ninicksicard/FFF_Free_Food_forever/docs/progression medias/100x+ spirulina microscope(streight strain) (1).jpg

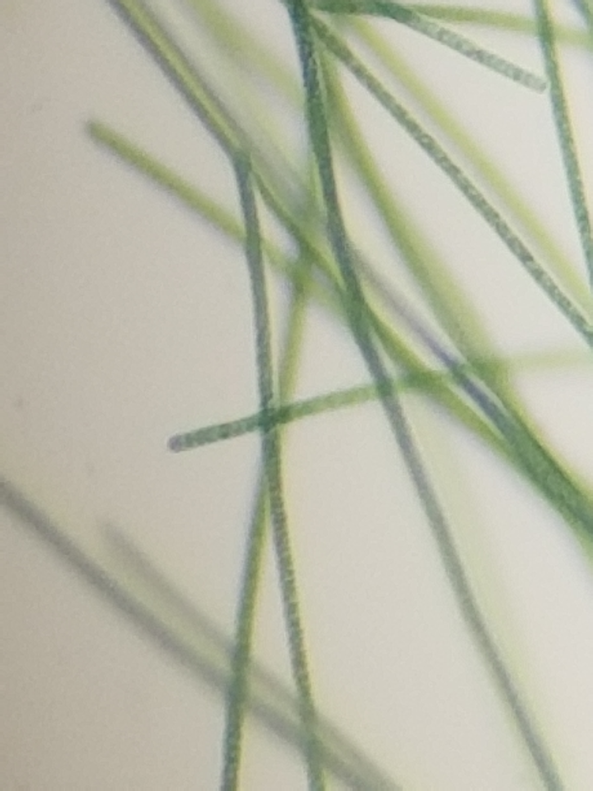
docs/progression medias/100x+ spirulina microscope(streight strain) (1).jpg
