ninicksicard/FFF_Free_Food_forever/docs/progression medias/100x+ spirulina microscope(streight strain) (2).jpg

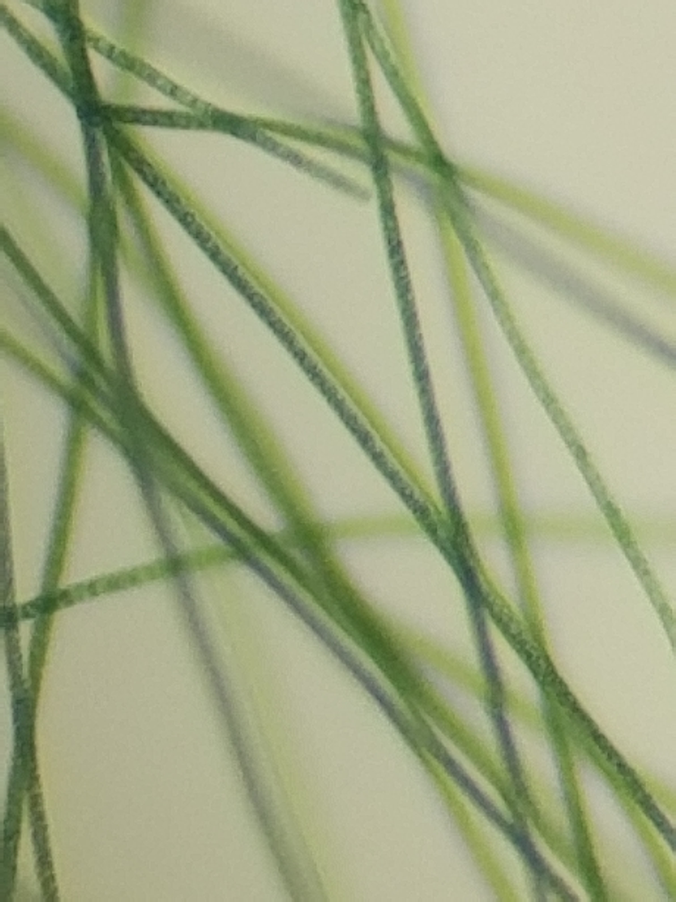
docs/progression medias/100x+ spirulina microscope(streight strain) (2).jpg
