ninicksicard/FFF_Free_Food_forever/docs/progression medias/20210616_152450.jpg

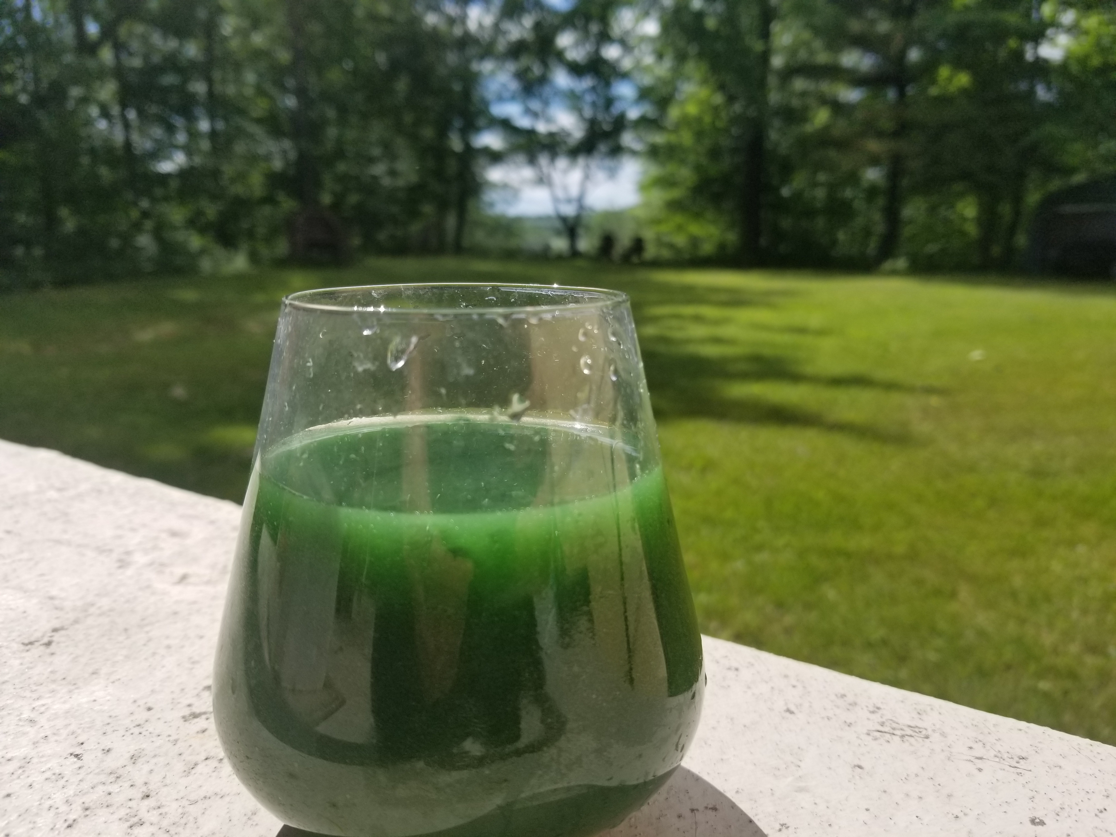
docs/progression medias/20210616_152450.jpg
