ninicksicard/FFF_Free_Food_forever/docs/progression medias/20210706_202033.jpg

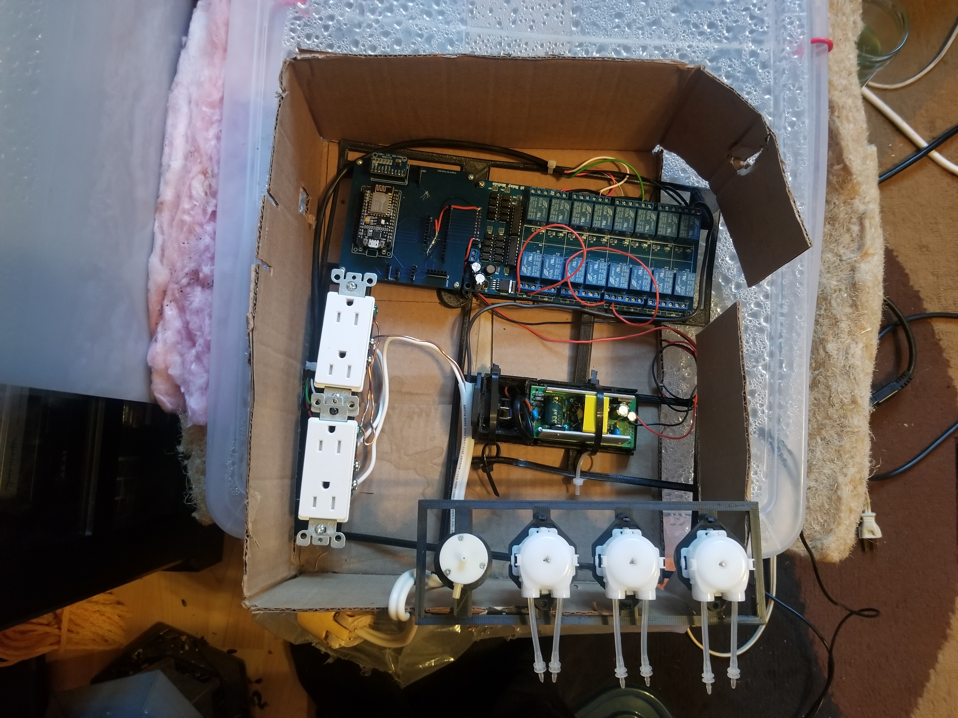
docs/progression medias/20210706_202033.jpg
