ninicksicard/FFF_Free_Food_forever/docs/progression medias/20210712_165235.jpg

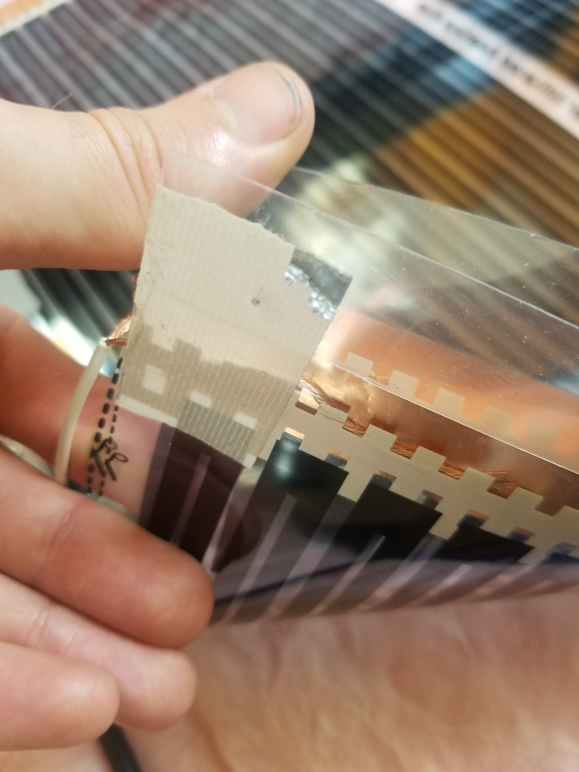
docs/progression medias/20210712_165235.jpg
