ninicksicard/FFF_Free_Food_forever/docs/progression medias/20210717_211324.jpg

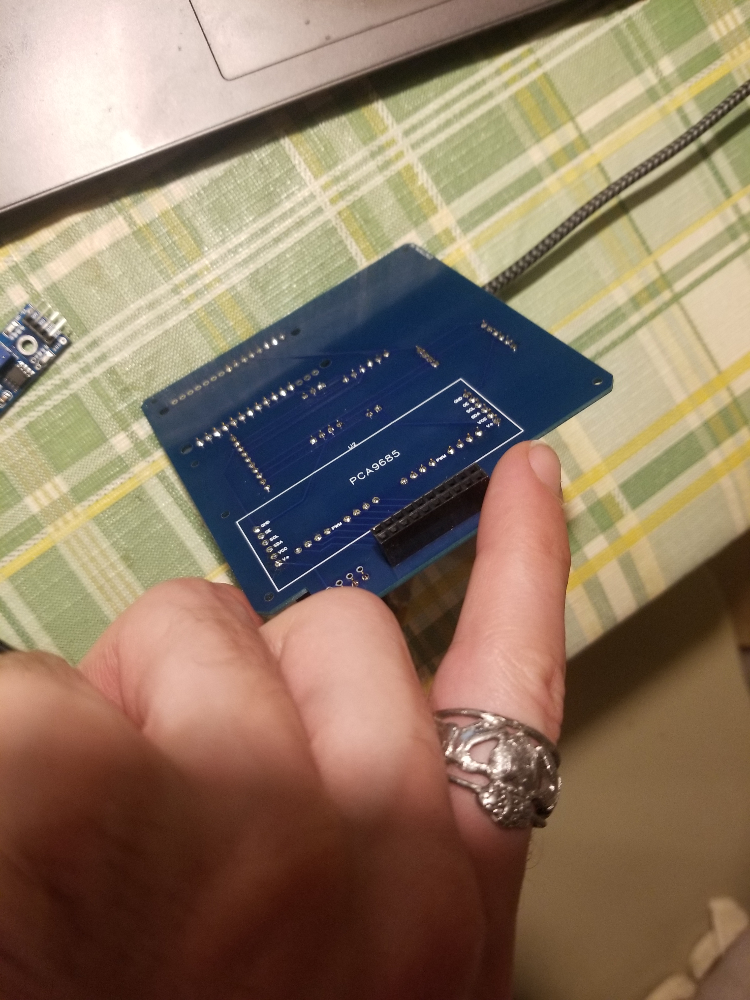
docs/progression medias/20210717_211324.jpg
