ninicksicard/FFF_Free_Food_forever/docs/progression medias/20210720_201423.jpg

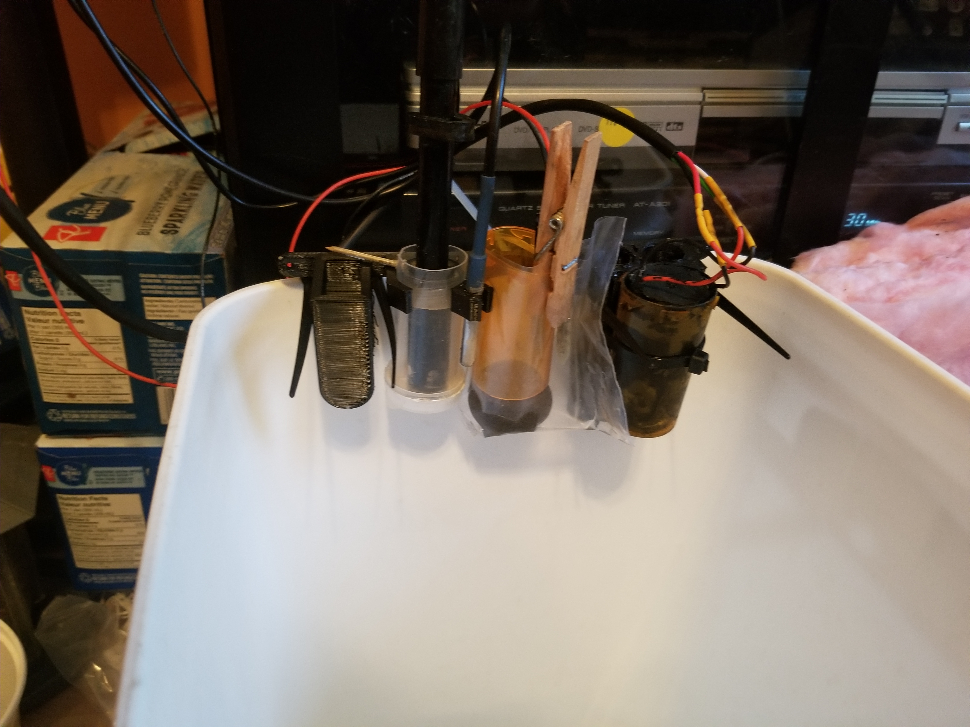
docs/progression medias/20210720_201423.jpg
