ninicksicard/FFF_Free_Food_forever/docs/progression medias/20210803_112624.jpg

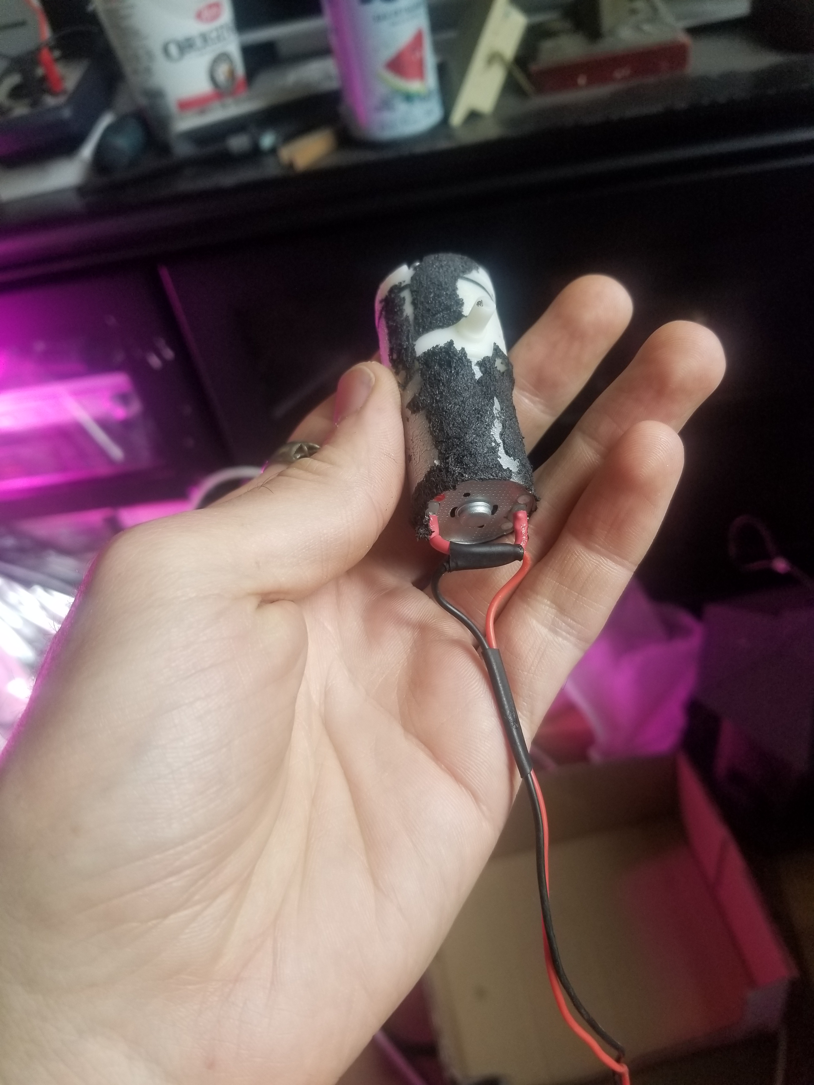
docs/progression medias/20210803_112624.jpg
