ninicksicard/FFF_Free_Food_forever/docs/progression medias/20220109_112840.jpg

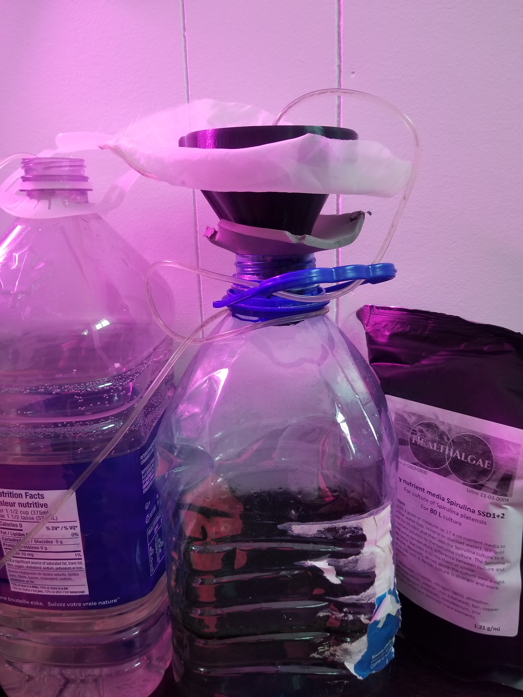
docs/progression medias/20220109_112840.jpg
