ninicksicard/FFF_Free_Food_forever/docs/progression medias/sample backup.jpg

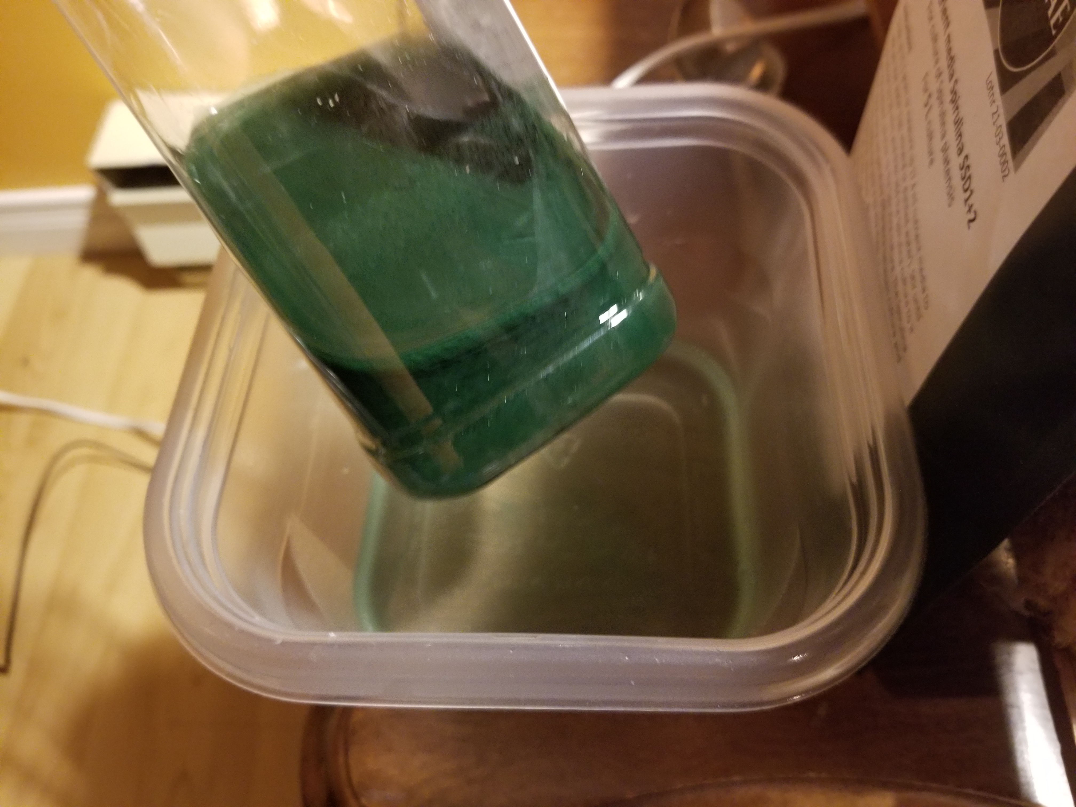
docs/progression medias/sample backup.jpg
