ninicksicard/FFF_Free_Food_forever/docs/progression medias/Screenshot_2.png

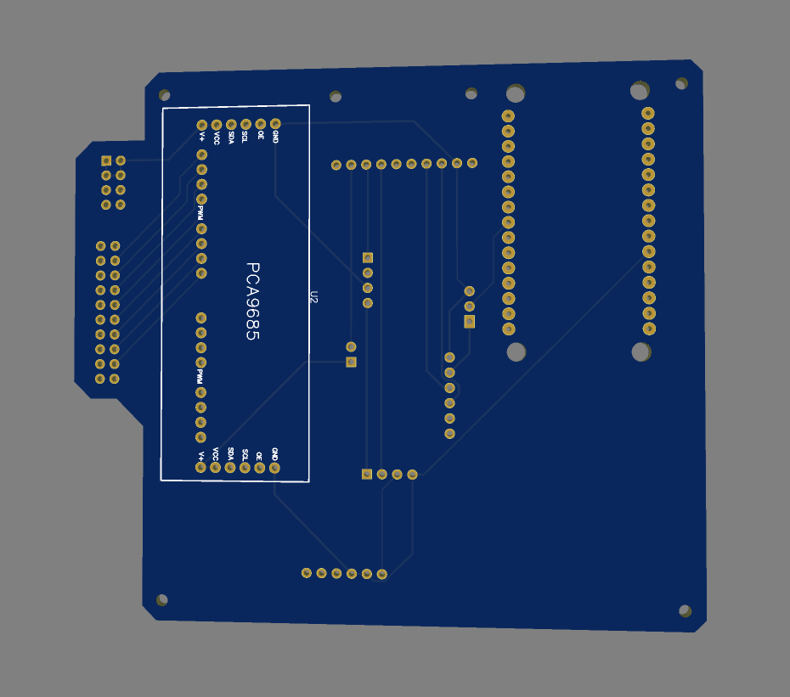
docs/progression medias/Screenshot_2.png
