ninicksicard/FFF_Free_Food_forever/docs/progression medias/Screenshot_4.png

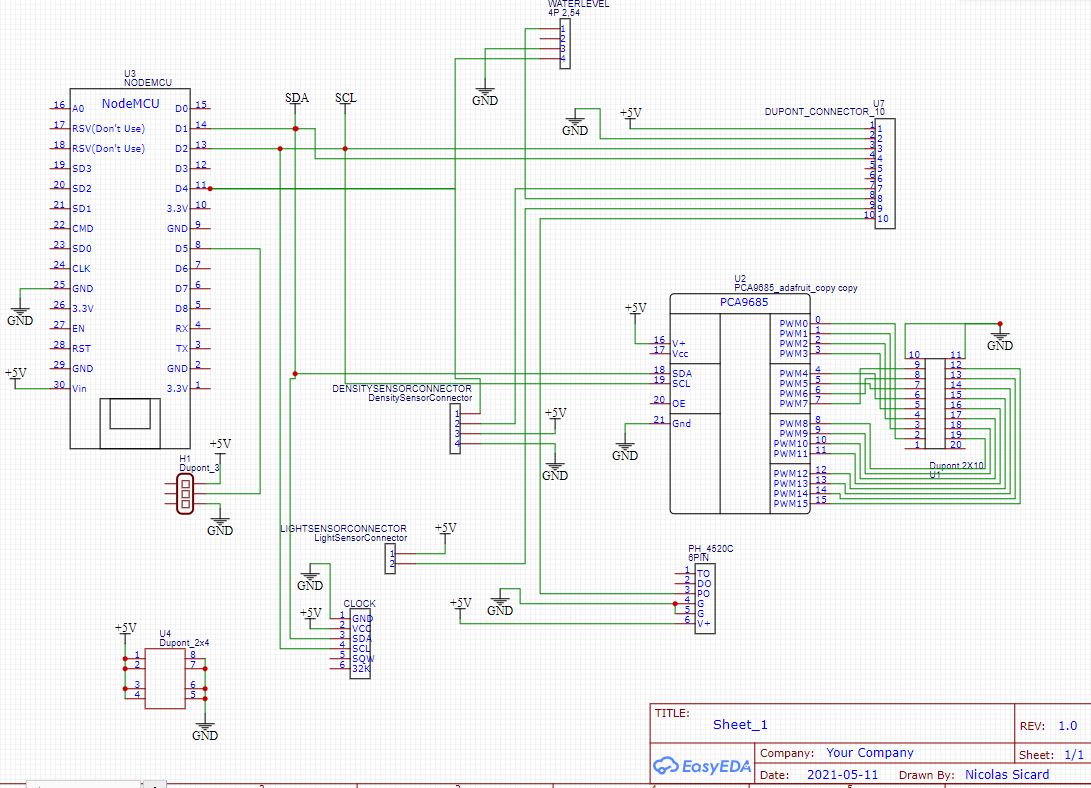
docs/progression medias/Screenshot_4.png
