ninicksicard/FFF_Free_Food_forever/Software/Screenshot_1.png

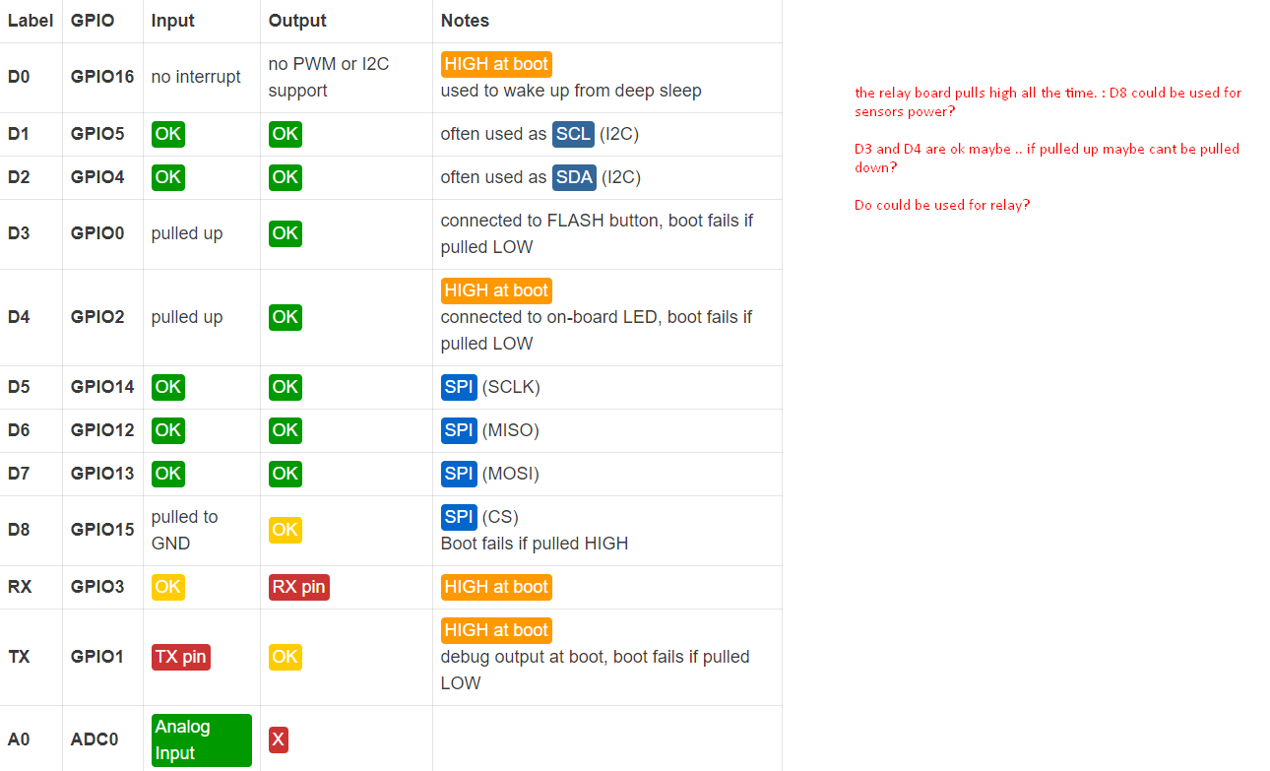
Software/Screenshot_1.png
