ninicksicard/FFF_Free_Food_forever/Hardware/STL/water_side - spacer_long-1.STL

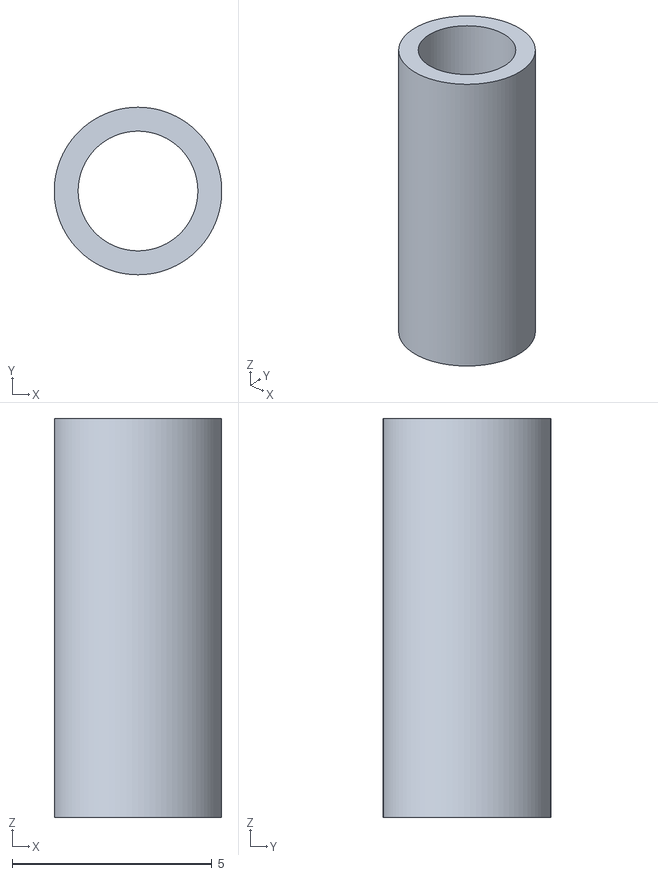
[picture p70: CAD file, 2022-02-06]
Hardware/STL/water_side - spacer_long-1.STL
4.20 x 4.20 x 10.0
