ninicksicard/FFF_Free_Food_forever/Hardware/STL/water_side - motor N20-2 spur gear_iso-4.STL

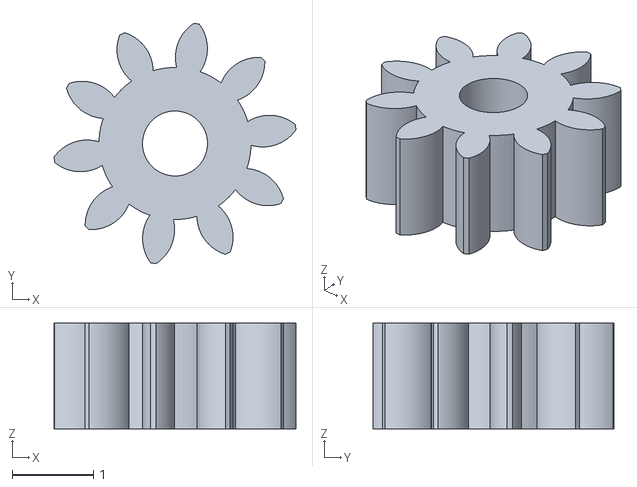
[picture p72: CAD file, 2022-02-06]
Hardware/STL/water_side - motor N20-2 spur gear_iso-4.STL
2.98 x 2.96 x 1.30
