ninicksicard/FFF_Free_Food_forever/Hardware/STL/water_side - spacer-1.STL

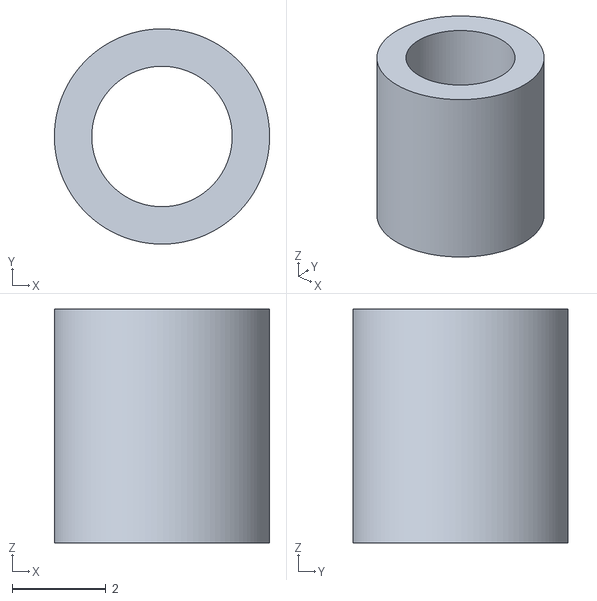
[picture p73: CAD file, 2022-02-06]
Hardware/STL/water_side - spacer-1.STL
4.60 x 4.60 x 5.00
