ninicksicard/FFF_Free_Food_forever/Hardware/STL/water_side - motor N20-2 втулка боковой шестерни-1.STL

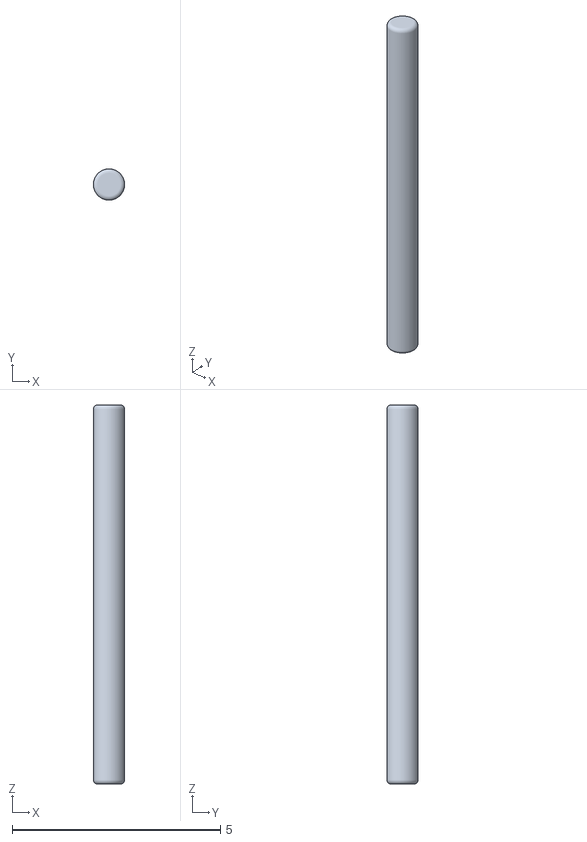
[picture p75: CAD file, 2022-02-06]
Hardware/STL/water_side - motor N20-2 втулка боковой шестерни-1.STL
0.75 x 0.75 x 9.10
