ninicksicard/FFF_Free_Food_forever/Hardware/STL/water_side - motor N20-2 spur gear_iso-9.STL

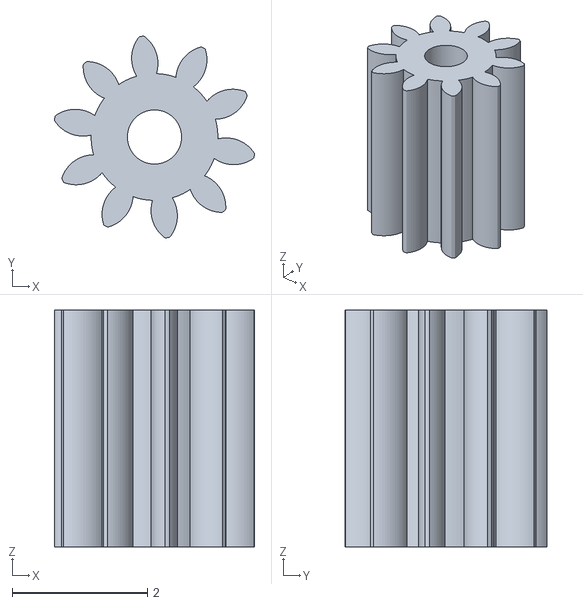
[picture p77: CAD file, 2022-02-06]
Hardware/STL/water_side - motor N20-2 spur gear_iso-9.STL
2.96 x 2.98 x 3.50
