ninicksicard/FFF_Free_Food_forever/Hardware/STL/water_side - motor N20-2 spur gear_iso-1.STL

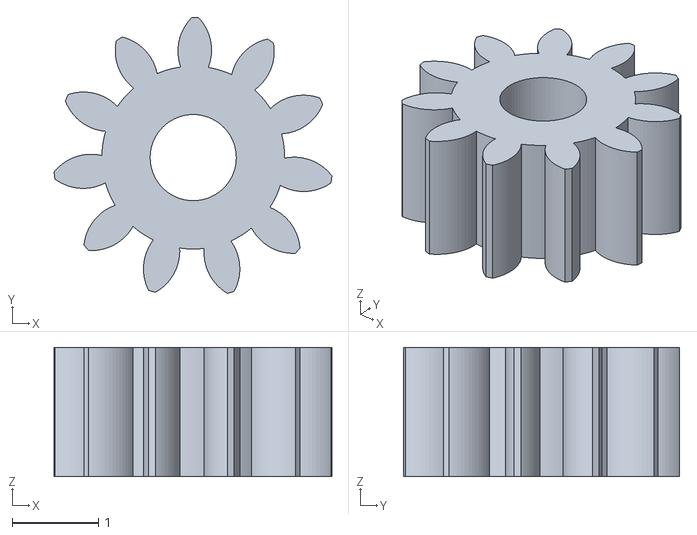
[picture p79: CAD file, 2022-02-06]
Hardware/STL/water_side - motor N20-2 spur gear_iso-1.STL
3.23 x 3.20 x 1.50
