ninicksicard/FFF_Free_Food_forever/Hardware/STL/water_side - motor N20-2 большая  фтулка-1.STL

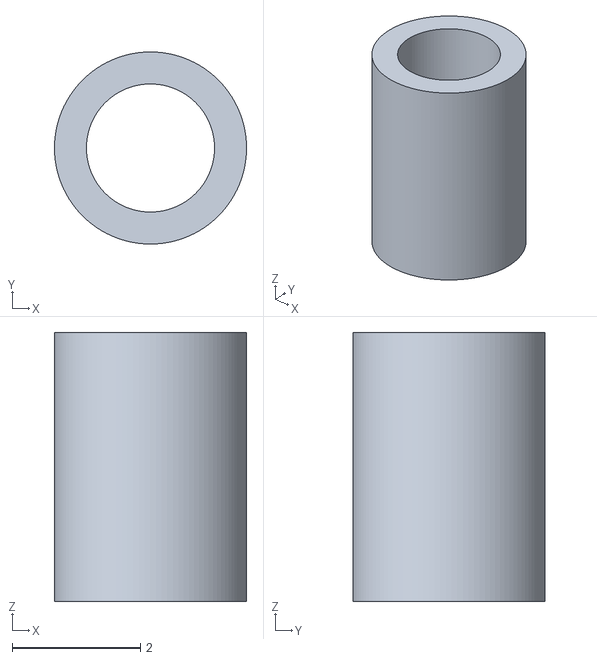
[picture p80: CAD file, 2022-02-06]
Hardware/STL/water_side - motor N20-2 большая фтулка-1.STL
3.00 x 3.00 x 4.20
