ninicksicard/FFF_Free_Food_forever/Hardware/STL/water_side - combinedmount-1.STL

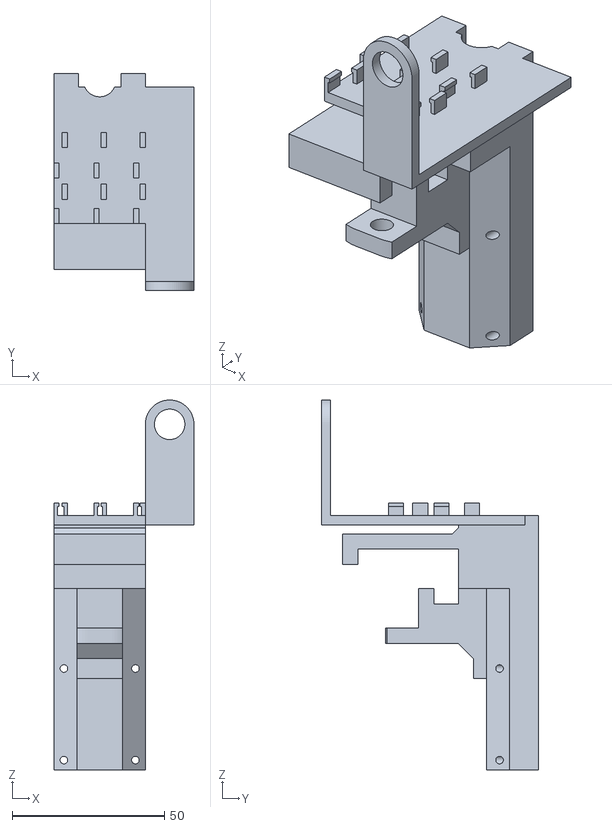
[picture p81: CAD file, 2022-02-06]
Hardware/STL/water_side - combinedmount-1.STL
46.0 x 71.4 x 121.6
