ninicksicard/FFF_Free_Food_forever/Hardware/STL/water_side - axel_connector-1.STL

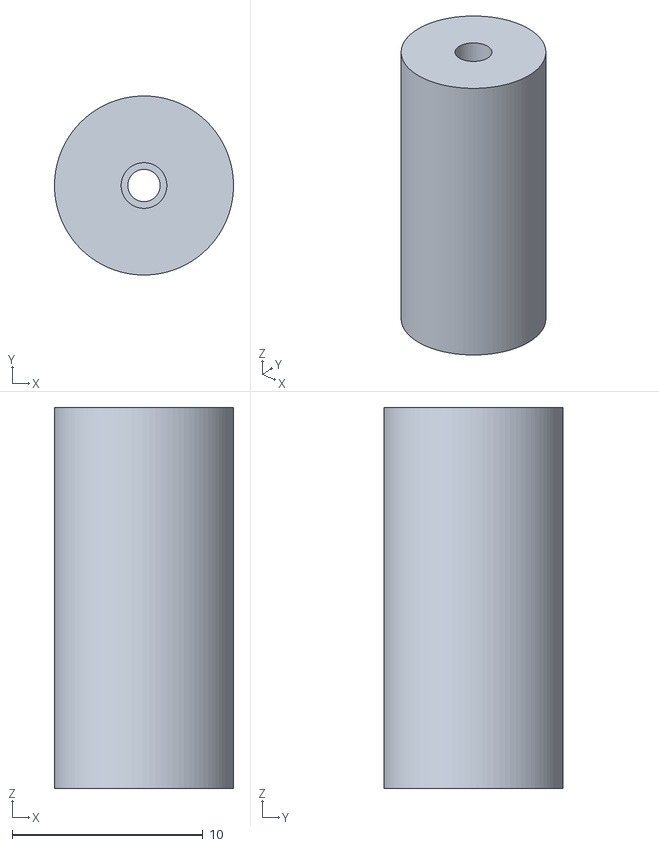
[picture p83: CAD file, 2022-02-06]
Hardware/STL/water_side - axel_connector-1.STL
9.40 x 9.40 x 20.0
