ninicksicard/FFF_Free_Food_forever/Hardware/STL/water_side - motor N20-2 верхняя пластина редуктора-1.STL

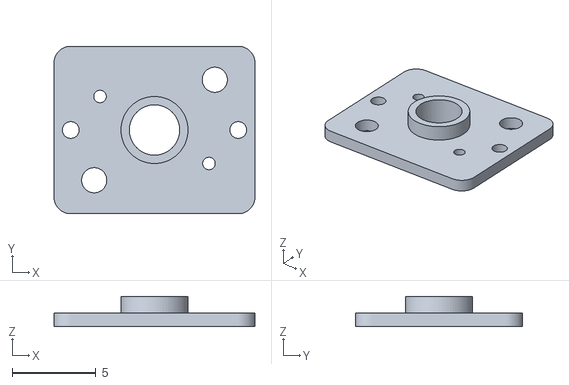
[picture p84: CAD file, 2022-02-06]
Hardware/STL/water_side - motor N20-2 верхняя пластина редуктора-1.STL
12.0 x 10.0 x 1.80
