ninicksicard/FFF_Free_Food_forever/Hardware/STL/water_side - Water_wheel_axel-1.STL

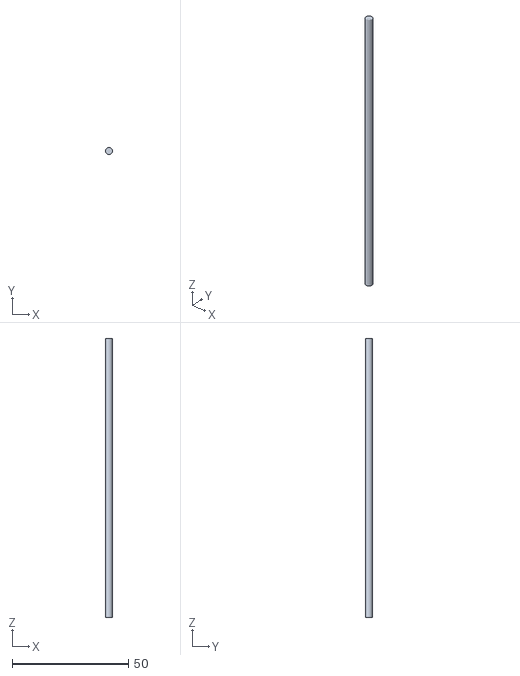
[picture p85: CAD file, 2022-02-06]
Hardware/STL/water_side - Water_wheel_axel-1.STL
3.00 x 3.00 x 120.0
