ninicksicard/FFF_Free_Food_forever/Hardware/STL/water_side - second_bearing_housing-1.STL

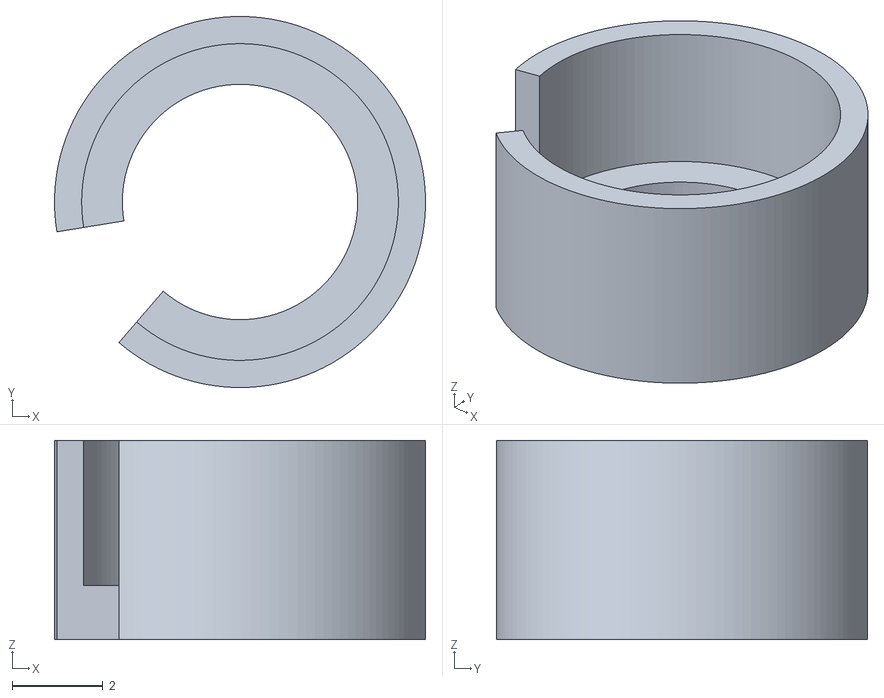
[picture p88: CAD file, 2022-02-06]
Hardware/STL/water_side - second_bearing_housing-1.STL
8.20 x 8.20 x 4.40
