ninicksicard/FFF_Free_Food_forever/Hardware/STL/water_side - motor N20-2 spur gear_iso-3.STL

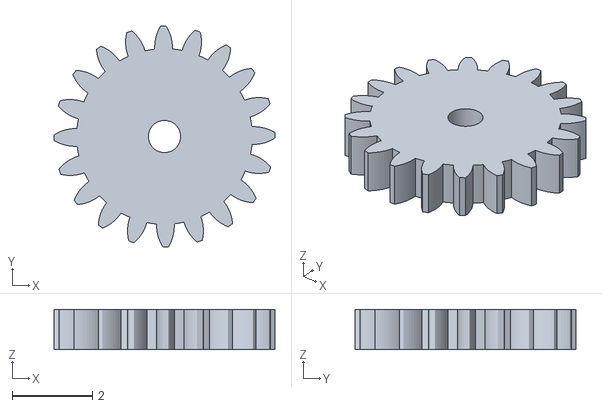
[picture p89: CAD file, 2022-02-06]
Hardware/STL/water_side - motor N20-2 spur gear_iso-3.STL
5.50 x 5.50 x 1.00
