ninicksicard/FFF_Free_Food_forever/Hardware/STL/water_side - bearing_mount-1.STL

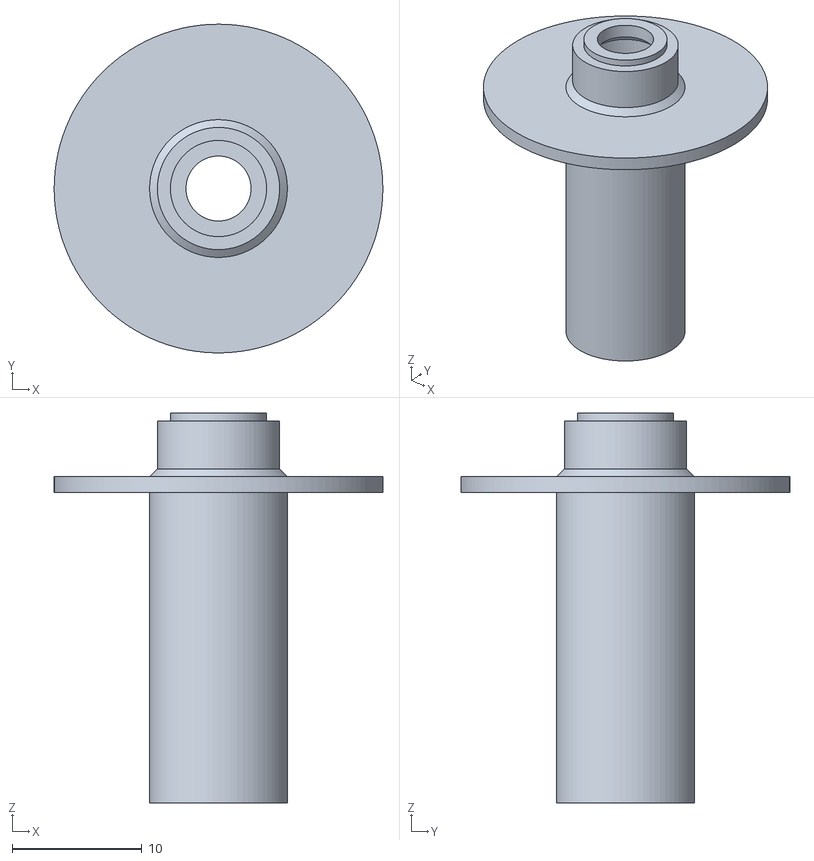
[picture p90: CAD file, 2022-02-06]
Hardware/STL/water_side - bearing_mount-1.STL
25.3 x 25.3 x 30.0
