ninicksicard/FFF_Free_Food_forever/Hardware/STL/System - highvoltage cable routing-1.STL

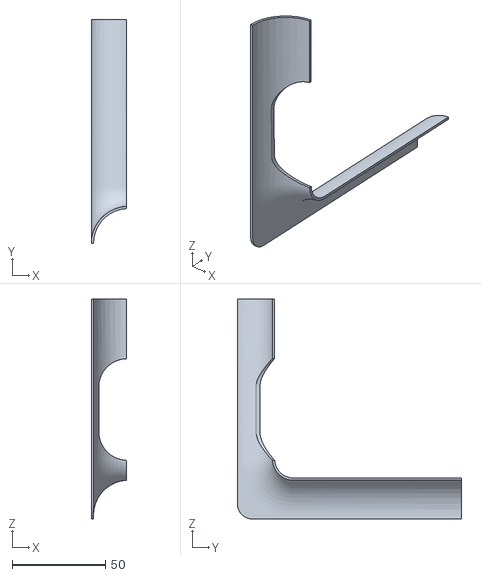
[picture p93: CAD file, 2022-01-04]
Hardware/STL/System - highvoltage cable routing-1.STL
19.0 x 120.2 x 117.9
