ninicksicard/FFF_Free_Food_forever/Hardware/STL/Sonsor Module  - densitysensor cappt2-1.STL

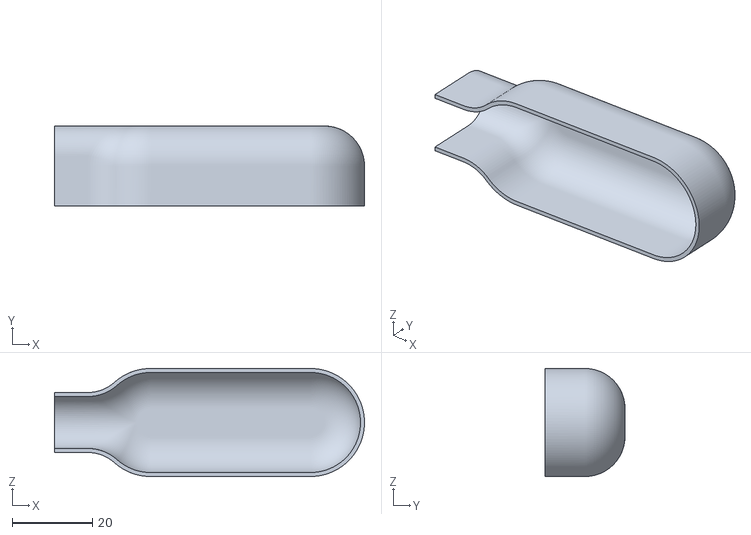
[picture p94: CAD file, 2022-01-04]
Hardware/STL/Sonsor Module - densitysensor cappt2-1.STL
77.5 x 20.0 x 27.0
