ninicksicard/FFF_Free_Food_forever/Hardware/STL/System - Part8-1.STL

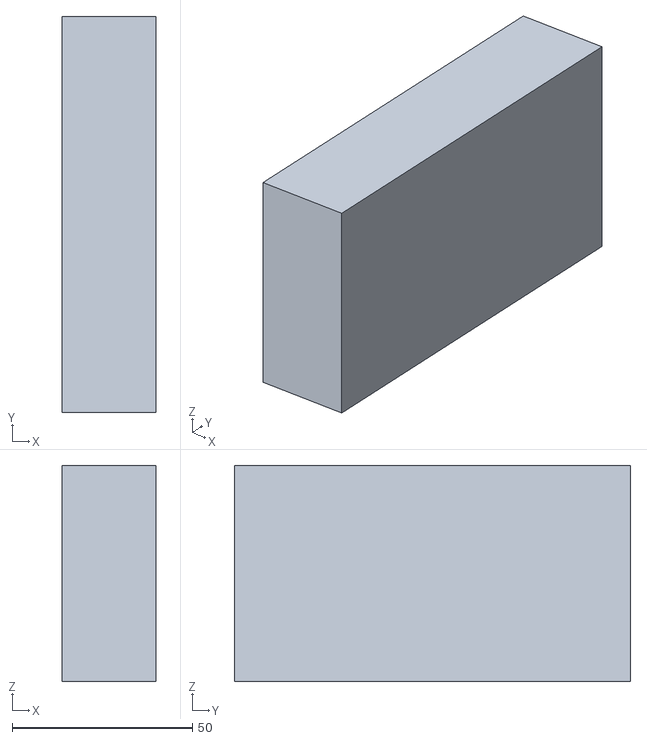
[picture p95: CAD file, 2022-01-04]
Hardware/STL/System - Part8-1.STL
26.0 x 110.0 x 60.0
