ninicksicard/FFF_Free_Food_forever/Hardware/STL/System - electronic case^System-1 Copy of Part5^electronic case_System-1.STL

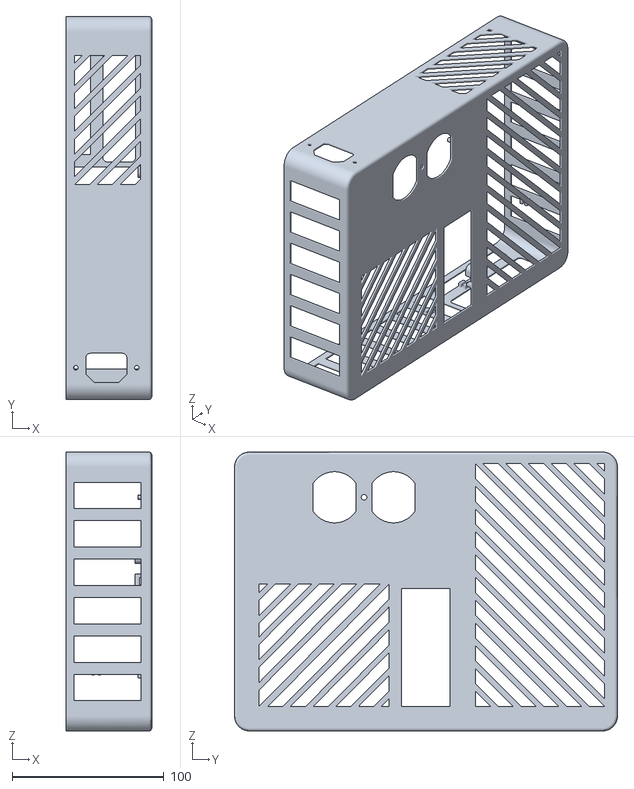
[picture p96: CAD file, 2022-01-04]
Hardware/STL/System - electronic case^System-1 Copy of Part5^electronic case_System-1.STL
56.5 x 252.5 x 183.9
