ninicksicard/FFF_Free_Food_forever/Hardware/STL/System - Part1-2.STL

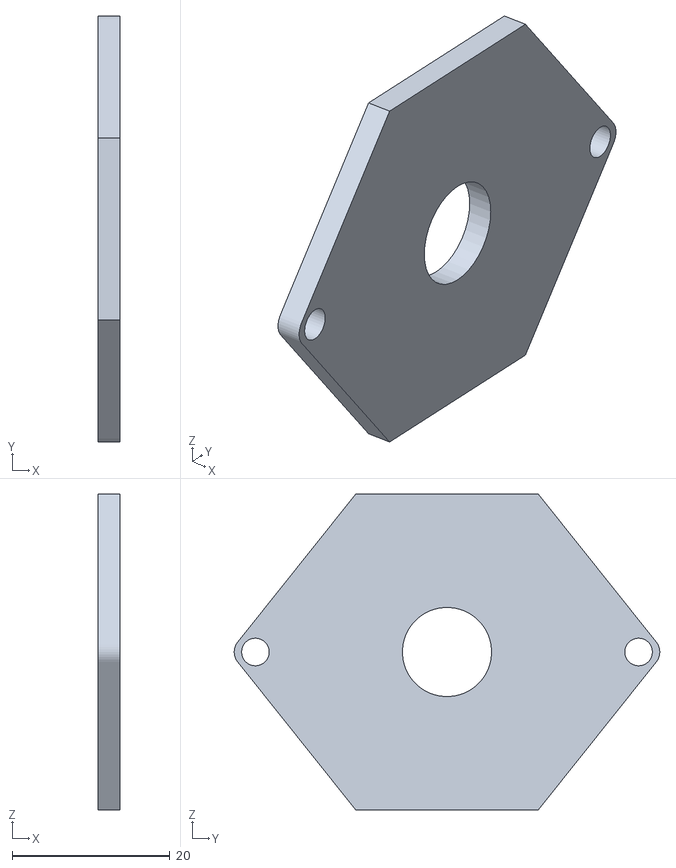
[picture p97: CAD file, 2022-01-04]
Hardware/STL/System - Part1-2.STL
2.80 x 53.9 x 40.0
