ninicksicard/FFF_Free_Food_forever/Hardware/STL/System - backplate-1.STL

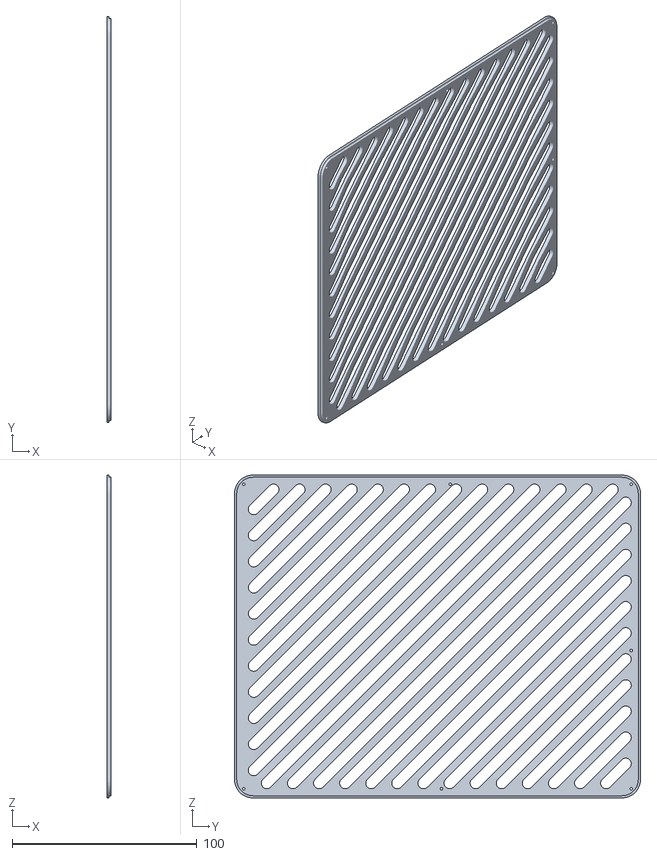
[picture p98: CAD file, 2022-01-04]
Hardware/STL/System - backplate-1.STL
2.40 x 220.0 x 175.0
