ninicksicard/FFF_Free_Food_forever/Hardware/STL/System - 7120K913_Straight-Blade Connector-1.STL

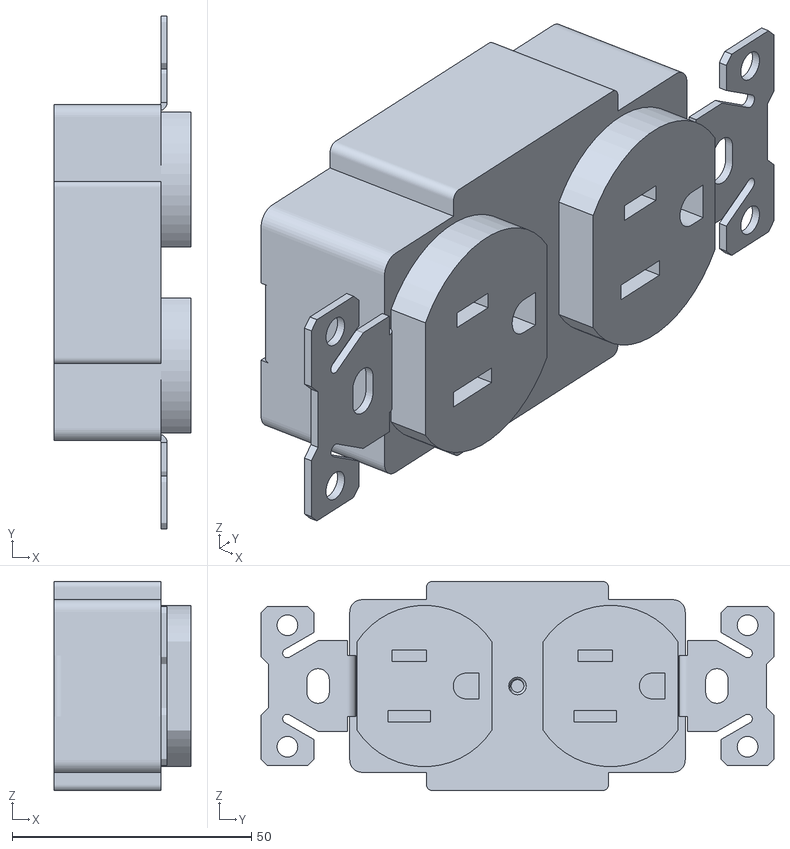
[picture p99: CAD file, 2022-01-04]
Hardware/STL/System - 7120K913_Straight-Blade Connector-1.STL
28.6 x 107.2 x 43.7
