ninicksicard/FFF_Free_Food_forever/Hardware/STL/System - high voltage covers-1.STL

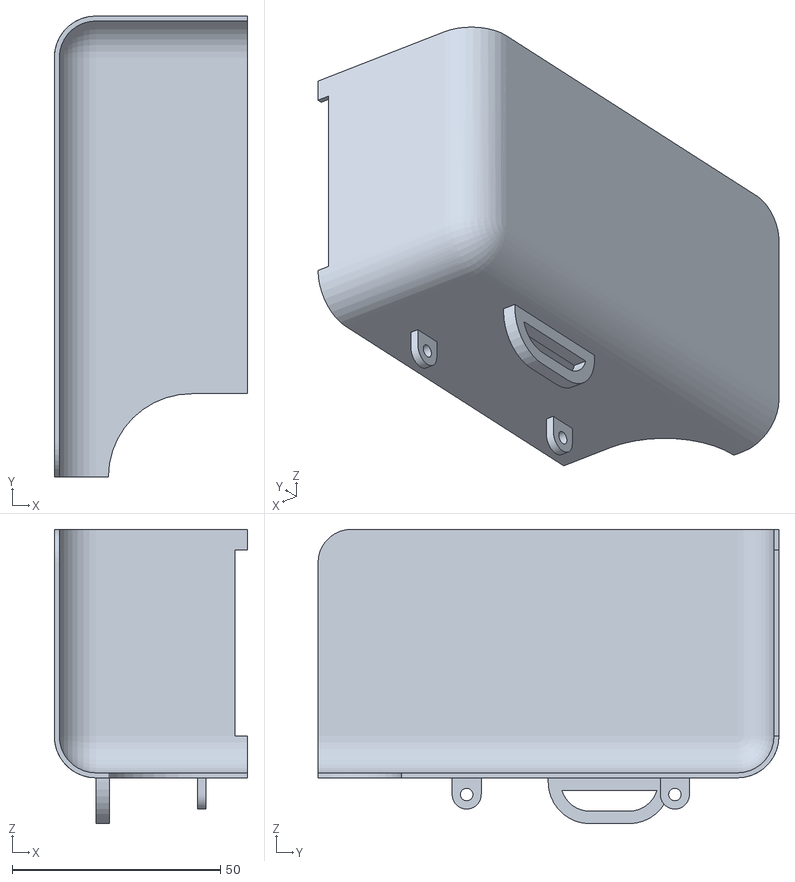
[picture p100: CAD file, 2022-01-04]
Hardware/STL/System - high voltage covers-1.STL
46.4 x 110.7 x 70.7
