ninicksicard/FFF_Free_Food_forever/Hardware/STL/System - 6331K85_Compact Round-Face DC Motor-2.STL

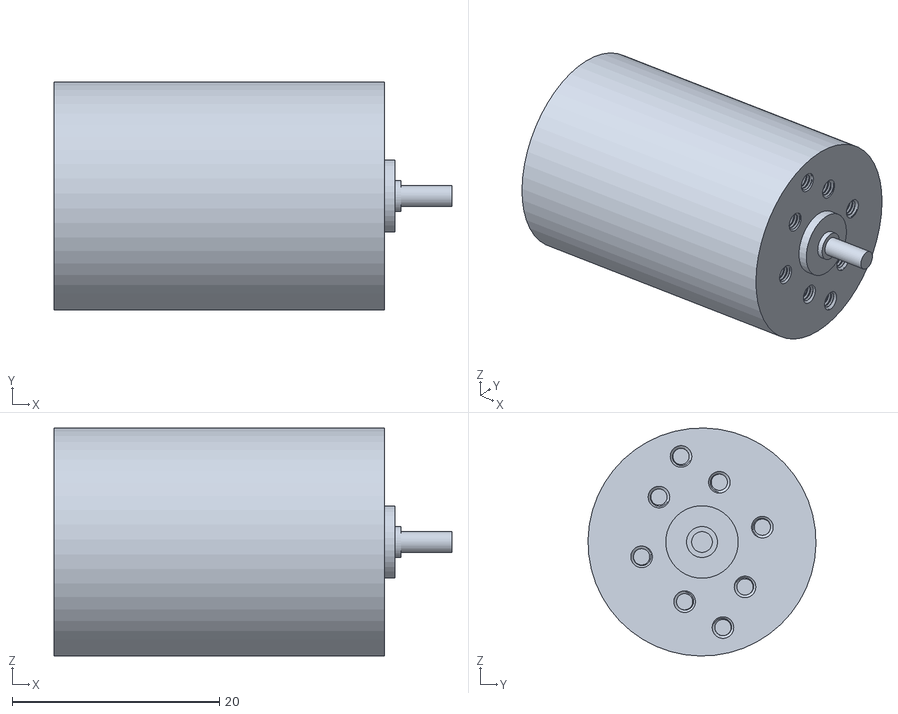
[picture p101: CAD file, 2022-01-04]
Hardware/STL/System - 6331K85_Compact Round-Face DC Motor-2.STL
38.4 x 22.0 x 22.0
