ninicksicard/FFF_Free_Food_forever/Hardware/STL/System - BoxCase-1.STL

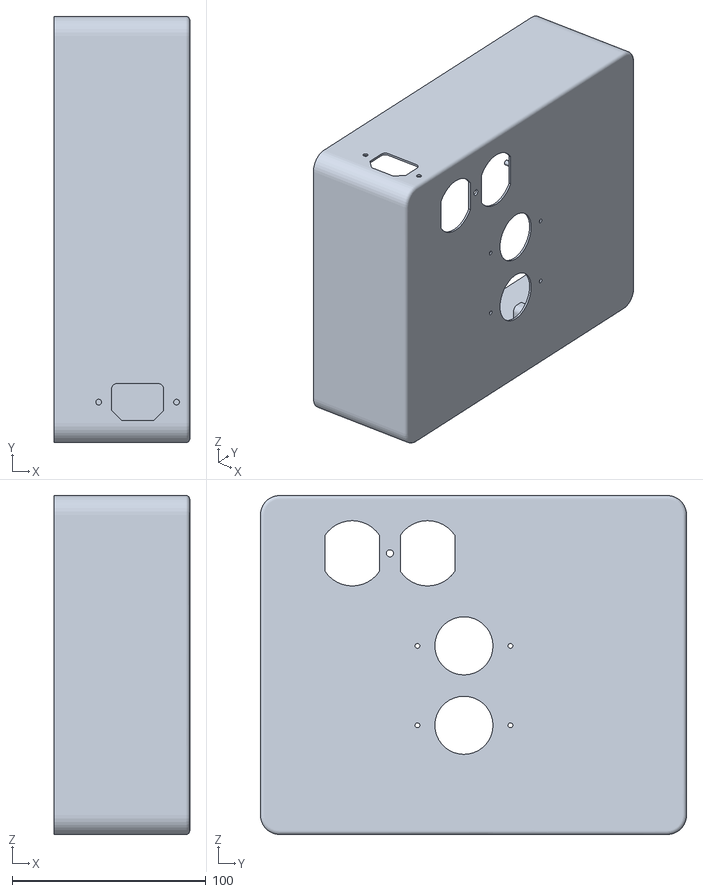
[picture p102: CAD file, 2022-01-04]
Hardware/STL/System - BoxCase-1.STL
70.0 x 220.0 x 175.0
