ninicksicard/FFF_Free_Food_forever/Hardware/STL/extraction_funnel.STL

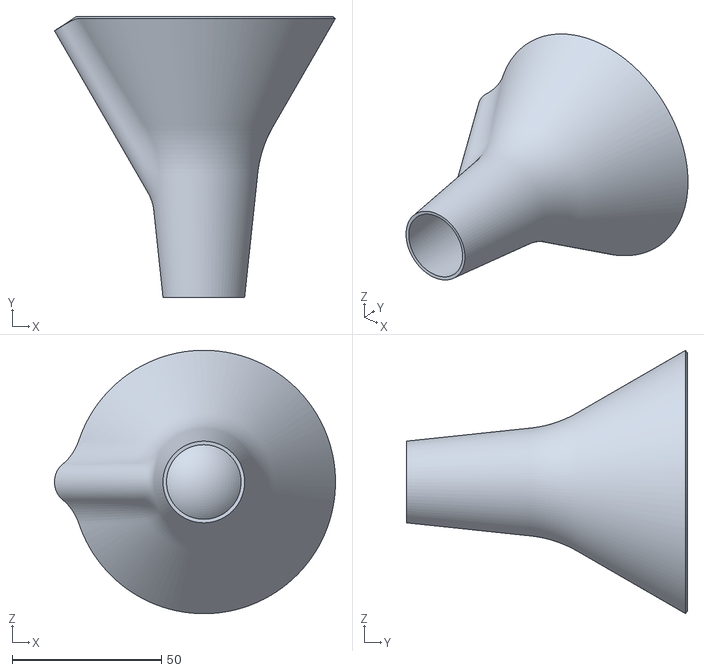
[picture p103: CAD file, 2022-01-04]
Hardware/STL/extraction_funnel.STL
94.2 x 94.3 x 88.3
