ninicksicard/FFF_Free_Food_forever/Hardware/STL/System - 4-Channel_Relay_Module_Mockup-1.STL

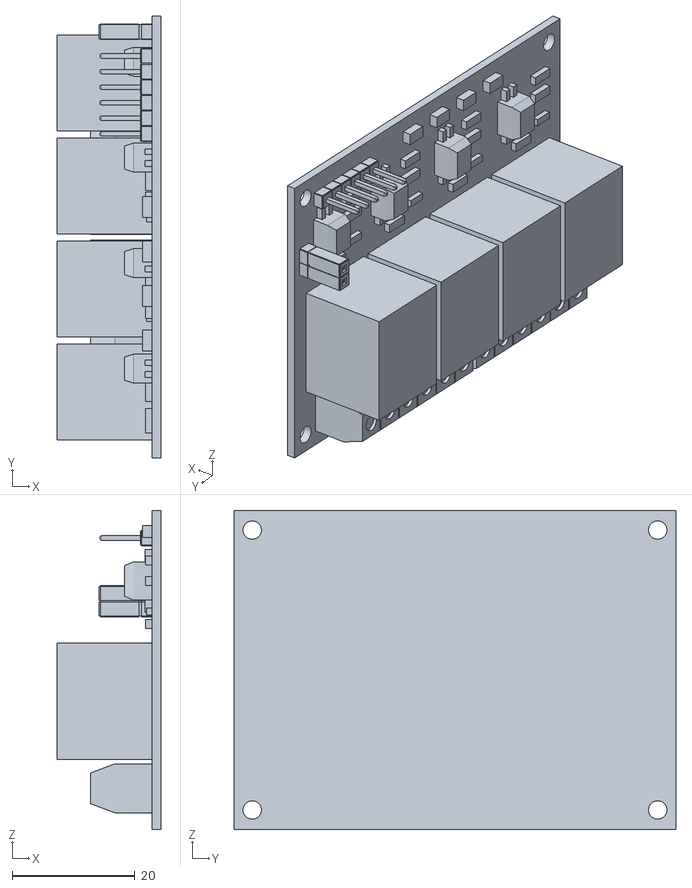
[picture p104: CAD file, 2022-01-04]
Hardware/STL/System - 4-Channel_Relay_Module_Mockup-1.STL
17.0 x 72.0 x 52.0
