ninicksicard/FFF_Free_Food_forever/Hardware/STL/Sonsor Module  - Sensor Module-1.STL

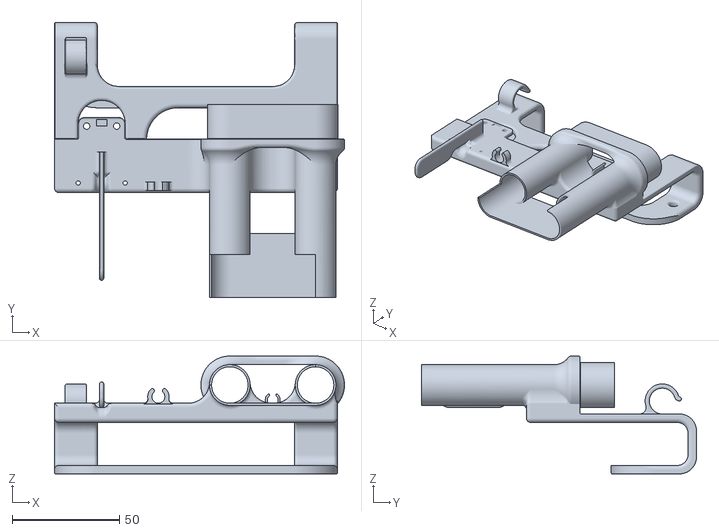
[picture p105: CAD file, 2022-01-04]
Hardware/STL/Sonsor Module - Sensor Module-1.STL
135.3 x 128.4 x 55.0
