ninicksicard/FFF_Free_Food_forever/Hardware/STL/Water_Level_sensor_floater - Part4^Water_Level_sensor_floater-1.STL

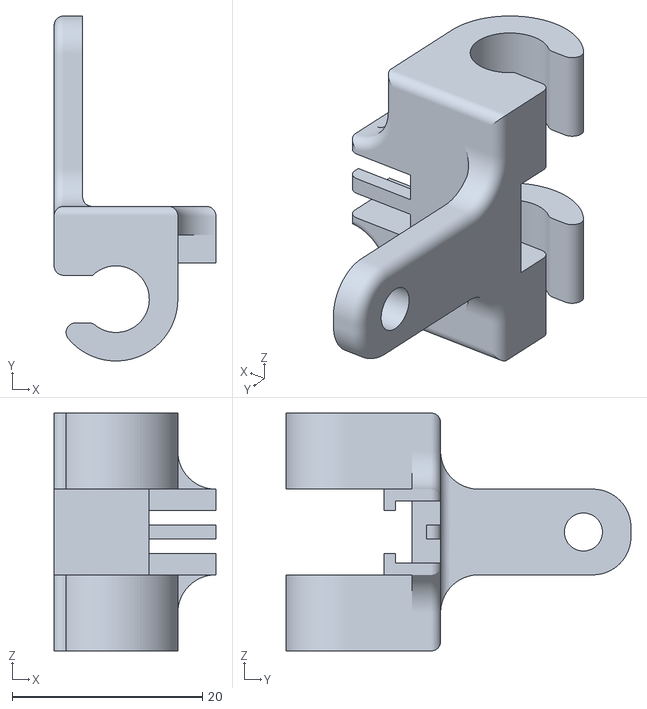
[picture p106: CAD file, 2022-01-04]
Hardware/STL/Water_Level_sensor_floater - Part4^Water_Level_sensor_floater-1.STL
17.0 x 36.2 x 25.0
