ninicksicard/FFF_Free_Food_forever/Hardware/STL/System - relaycontrolercover-1.STL

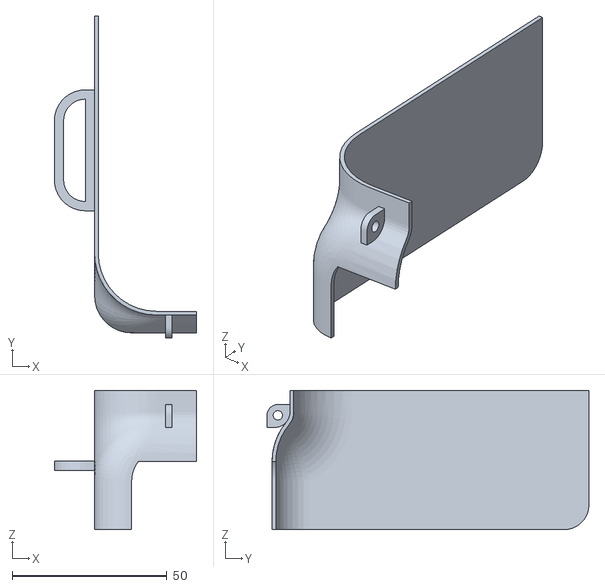
[picture p107: CAD file, 2022-01-04]
Hardware/STL/System - relaycontrolercover-1.STL
46.0 x 104.1 x 45.0
