ninicksicard/FFF_Free_Food_forever/Hardware/STL/System - OBJ_FFF_PCB-1.STL

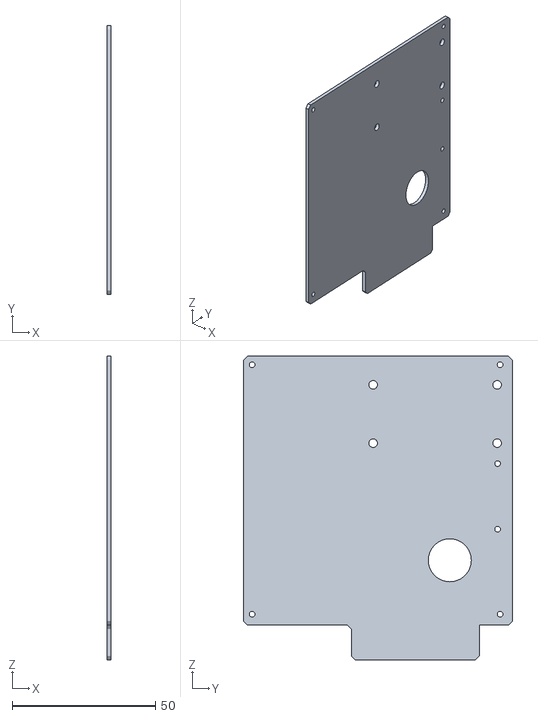
[picture p108: CAD file, 2022-01-04]
Hardware/STL/System - OBJ_FFF_PCB-1.STL
1.50 x 93.9 x 106.1
