ninicksicard/FFF_Free_Food_forever/Hardware/STL/extraction_funnel_cover.STL

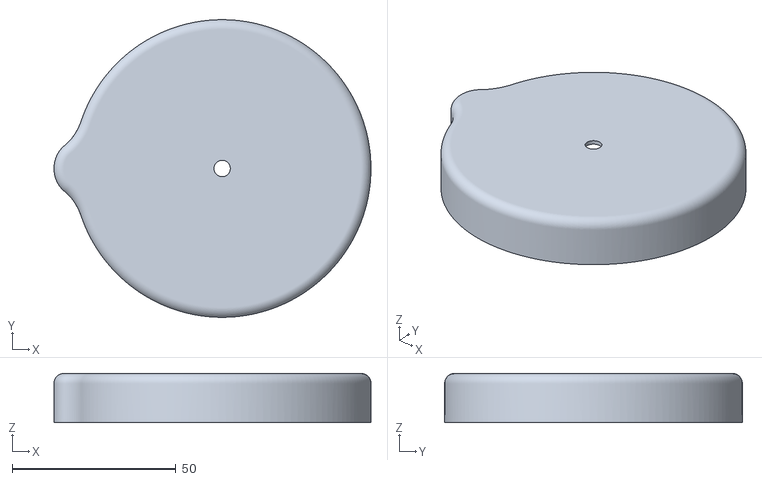
[picture p109: CAD file, 2022-01-04]
Hardware/STL/extraction_funnel_cover.STL
96.9 x 91.0 x 15.0
