ninicksicard/FFF_Free_Food_forever/Hardware/STL/System - PowerSuply_Placeholder_good-1.STL

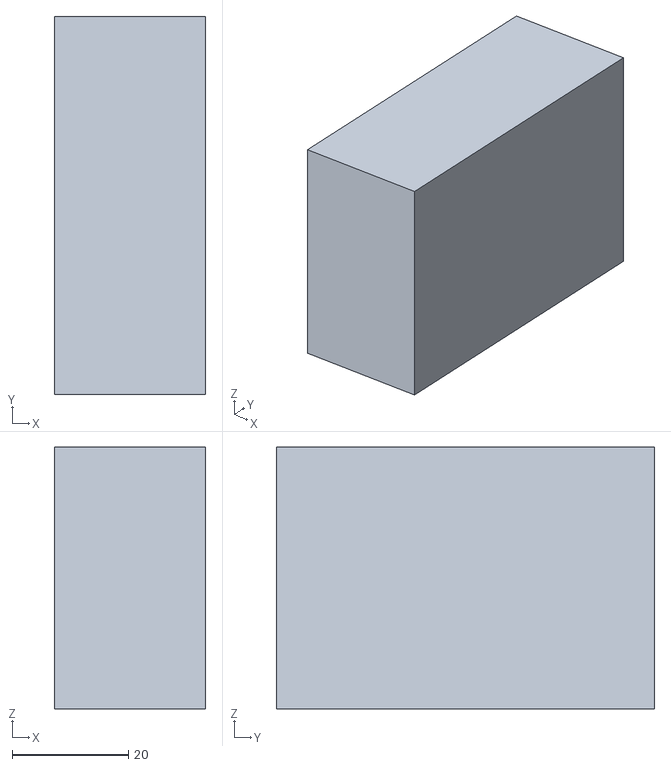
[picture p110: CAD file, 2022-01-04]
Hardware/STL/System - PowerSuply_Placeholder_good-1.STL
26.0 x 65.0 x 45.0
