ninicksicard/FFF_Free_Food_forever/Hardware/STL/Sonsor Module  - DensitysensorCappt1-1.STL

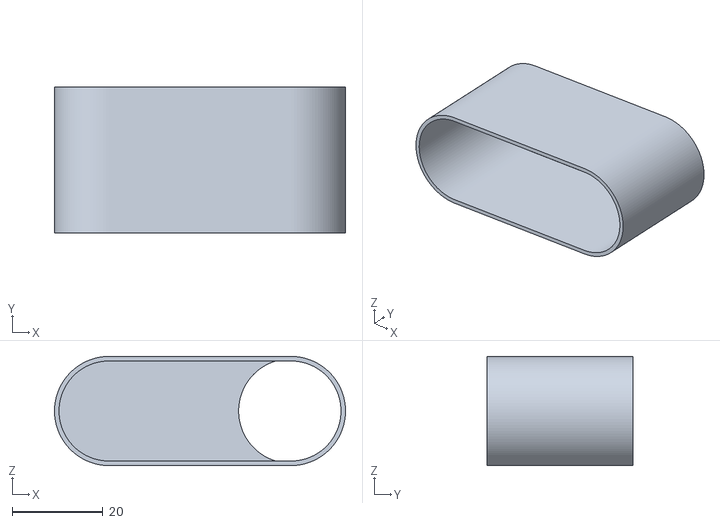
[picture p111: CAD file, 2022-01-04]
Hardware/STL/Sonsor Module - DensitysensorCappt1-1.STL
64.0 x 32.0 x 24.0
