ninicksicard/FFF_Free_Food_forever/Hardware/STL/electronic frame mount - DensitysensorCappt1-1.STL

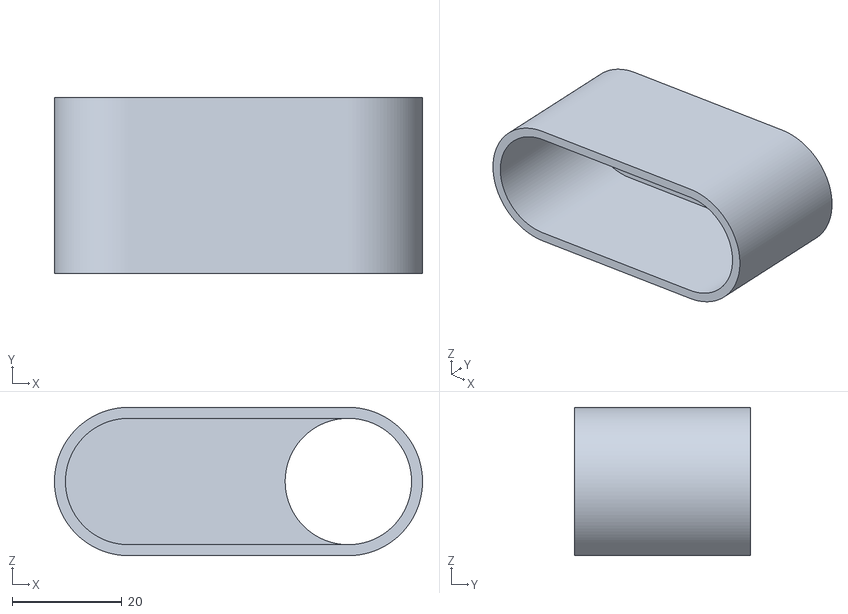
[picture p112: CAD file, 2021-08-17]
Hardware/STL/electronic frame mount - DensitysensorCappt1-1.STL
67.0 x 32.0 x 27.0
