ninicksicard/FFF_Free_Food_forever/Hardware/STL/electronic frame mount - densitysensor cappt2-1.STL

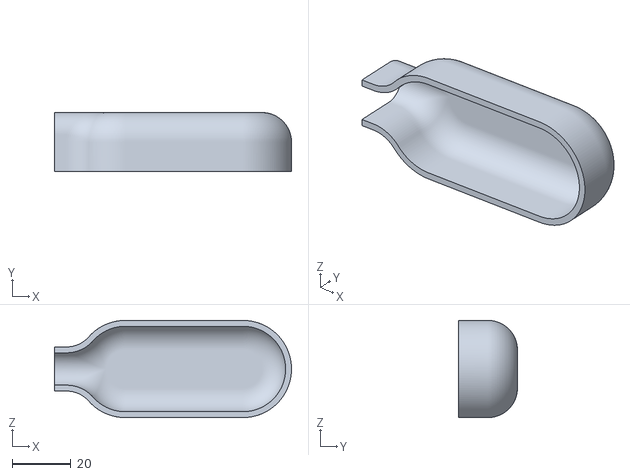
[picture p113: CAD file, 2021-08-17]
Hardware/STL/electronic frame mount - densitysensor cappt2-1.STL
80.5 x 20.0 x 33.0
