ninicksicard/FFF_Free_Food_forever/Hardware/STL/electronic frame mount - Sensor Module-1.STL

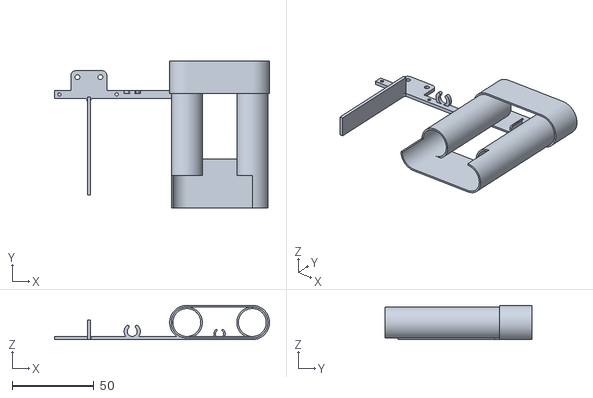
[picture p114: CAD file, 2021-08-17]
Hardware/STL/electronic frame mount - Sensor Module-1.STL
131.3 x 90.0 x 21.0
