ninicksicard/FFF_Free_Food_forever/Hardware/STL/saltspoon.STL

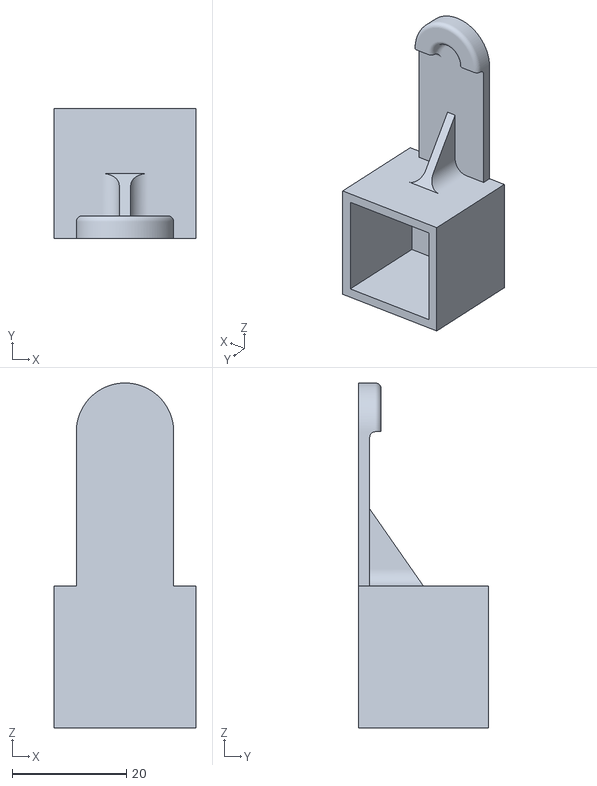
[picture p115: CAD file, 2021-08-15]
Hardware/STL/saltspoon.STL
24.8 x 22.8 x 60.3
