ninicksicard/FFF_Free_Food_forever/Hardware/STL/electronic frame.STL

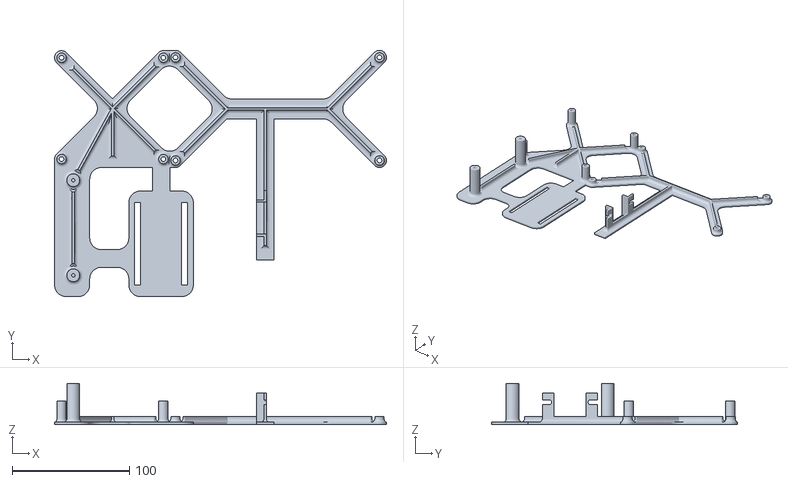
[picture p116: CAD file, 2021-08-15]
Hardware/STL/electronic frame.STL
282.8 x 209.8 x 35.0
