ninicksicard/FFF_Free_Food_forever/Hardware/STL/Sensor Module.STL

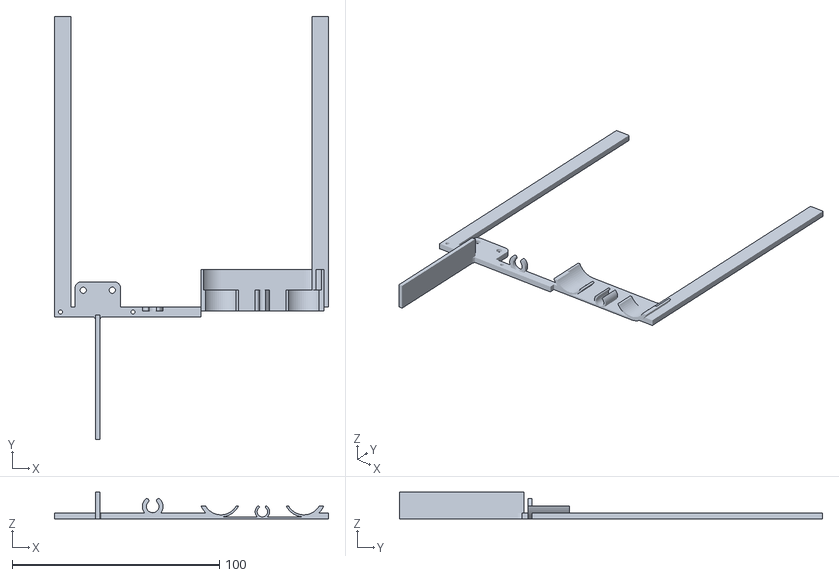
[picture p117: CAD file, 2021-08-15]
Hardware/STL/Sensor Module.STL
132.4 x 204.0 x 13.0
