ninicksicard/FFF_Free_Food_forever/Hardware/STL/fertilizerspoon.STL

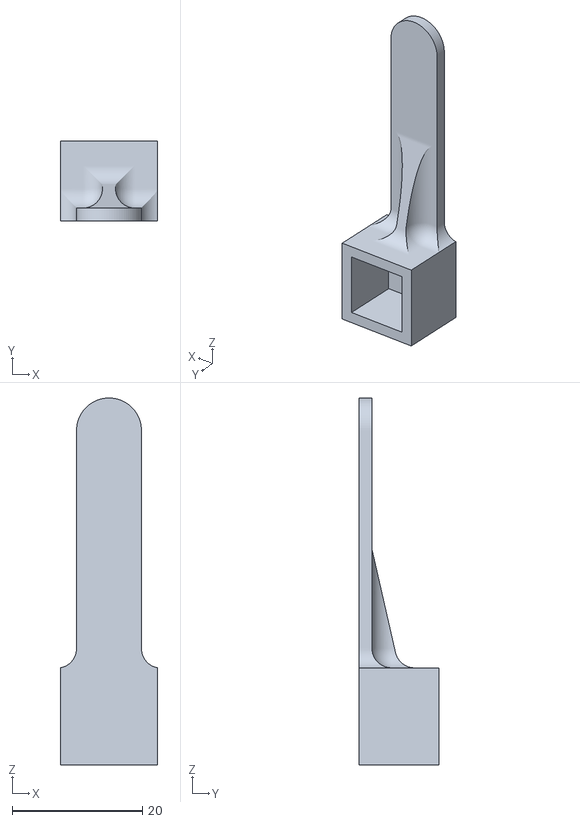
[picture p118: CAD file, 2021-08-15]
Hardware/STL/fertilizerspoon.STL
14.9 x 12.3 x 56.3
