ninicksicard/FFF_Free_Food_forever/Hardware/STL/SodiumBicaronatepoon.STL

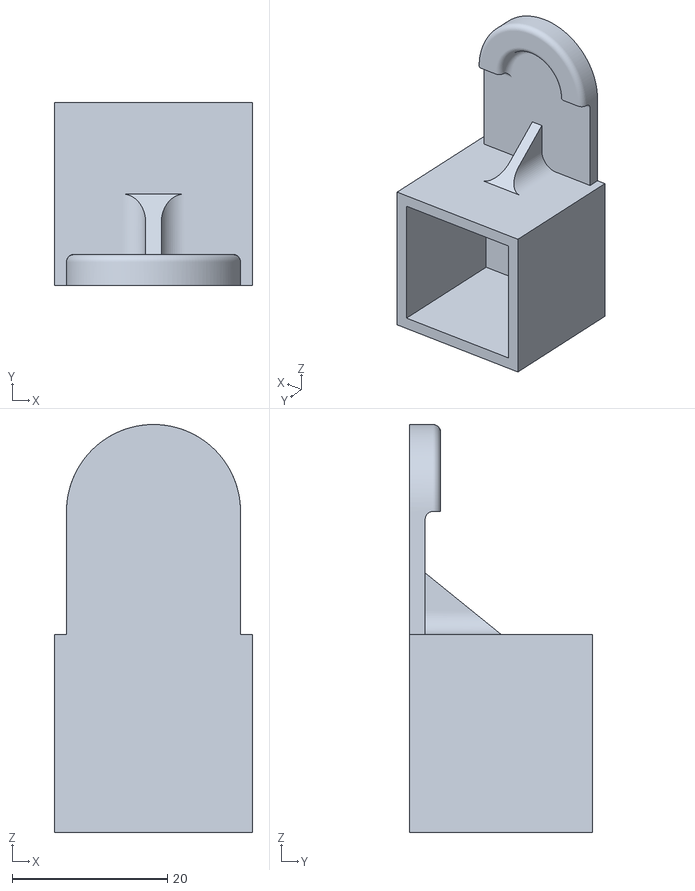
[picture p119: CAD file, 2021-08-15]
Hardware/STL/SodiumBicaronatepoon.STL
25.5 x 23.5 x 52.6
