ninicksicard/FFF_Free_Food_forever/Hardware/STL/extraction.STL

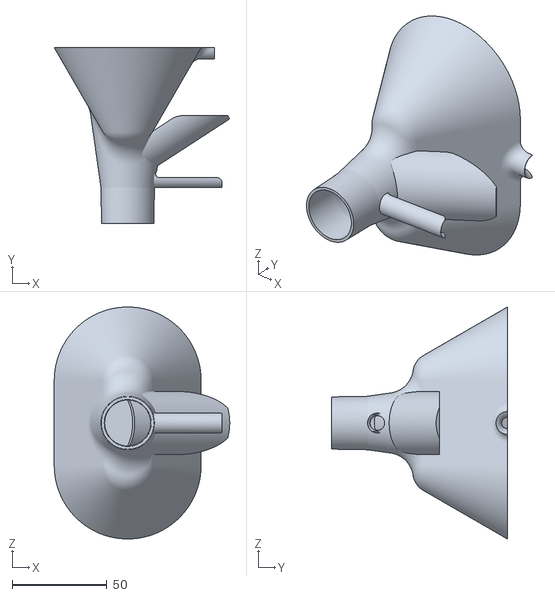
[picture p120: CAD file, 2021-08-15]
Hardware/STL/extraction.STL
92.9 x 93.0 x 122.7
