ninicksicard/FFF_Free_Food_forever/Hardware/STL/Extractor^Bioreactor - Copy of Part7^Extractor_Bioreactor-1.STL

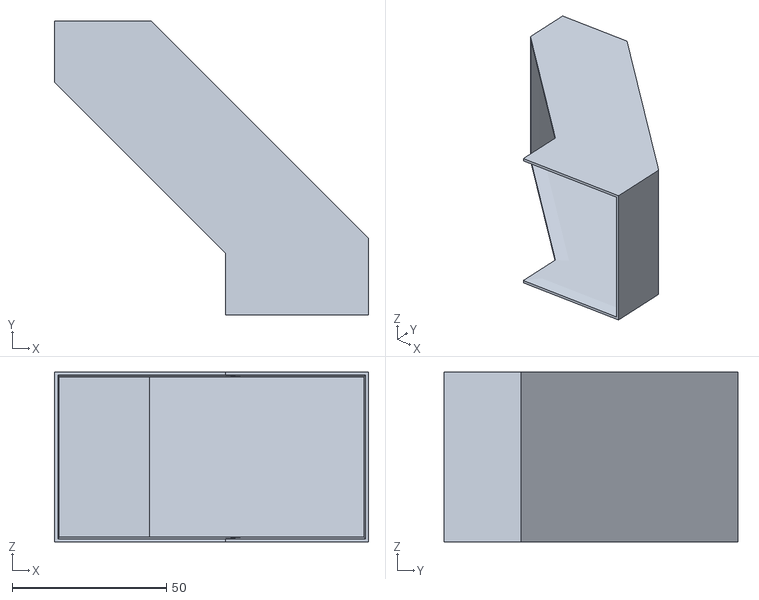
[picture p121: CAD file, 2021-07-31]
Hardware/STL/Extractor^Bioreactor - Copy of Part7^Extractor_Bioreactor-1.STL
101.8 x 95.4 x 55.0
