ninicksicard/FFF_Free_Food_forever/Hardware/STL/sensors moduleframe.STL

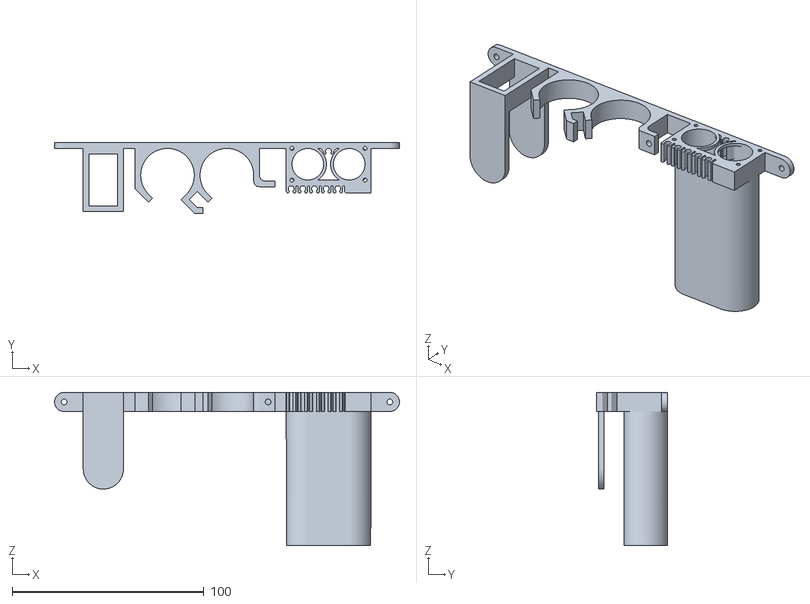
[picture p122: CAD file, 2021-07-31]
Hardware/STL/sensors moduleframe.STL
180.1 x 36.9 x 80.0
