ninicksicard/FFF_Free_Food_forever/Hardware/STL/filterv3 - filterv3-1.STL

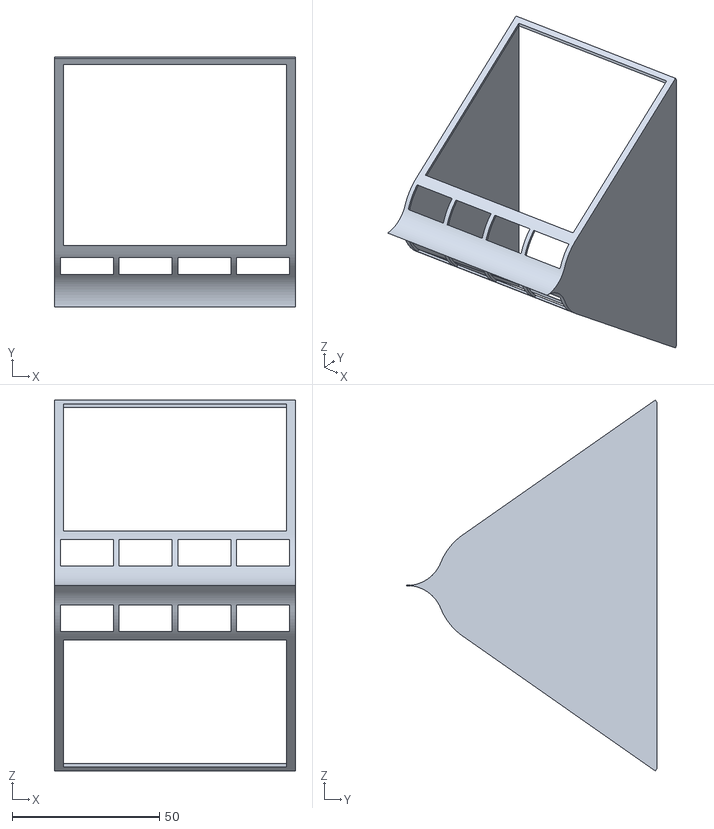
[picture p123: CAD file, 2021-07-31]
Hardware/STL/filterv3 - filterv3-1.STL
82.0 x 85.1 x 126.2
