ninicksicard/FFF_Free_Food_forever/Hardware/STL/Extractor^Bioreactor - Copy of Part1^Extractor_Bioreactor-1.STL

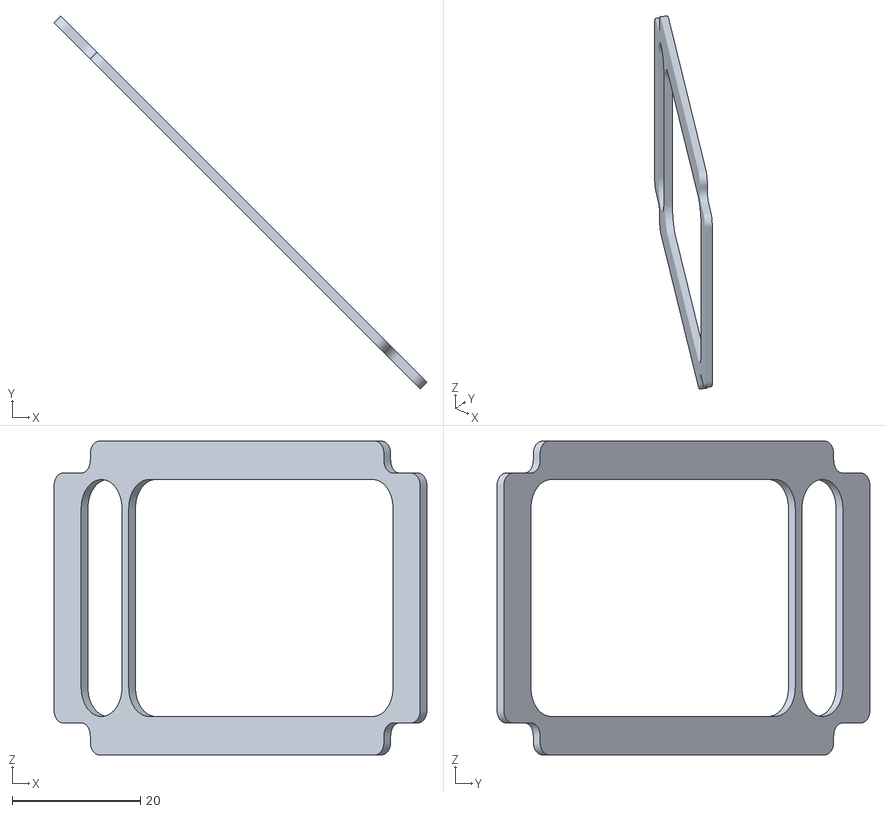
[picture p124: CAD file, 2021-07-31]
Hardware/STL/Extractor^Bioreactor - Copy of Part1^Extractor_Bioreactor-1.STL
58.2 x 58.2 x 49.0
