ninicksicard/FFF_Free_Food_forever/Hardware/STL/filterv3 - Part2^filterv3-1.STL

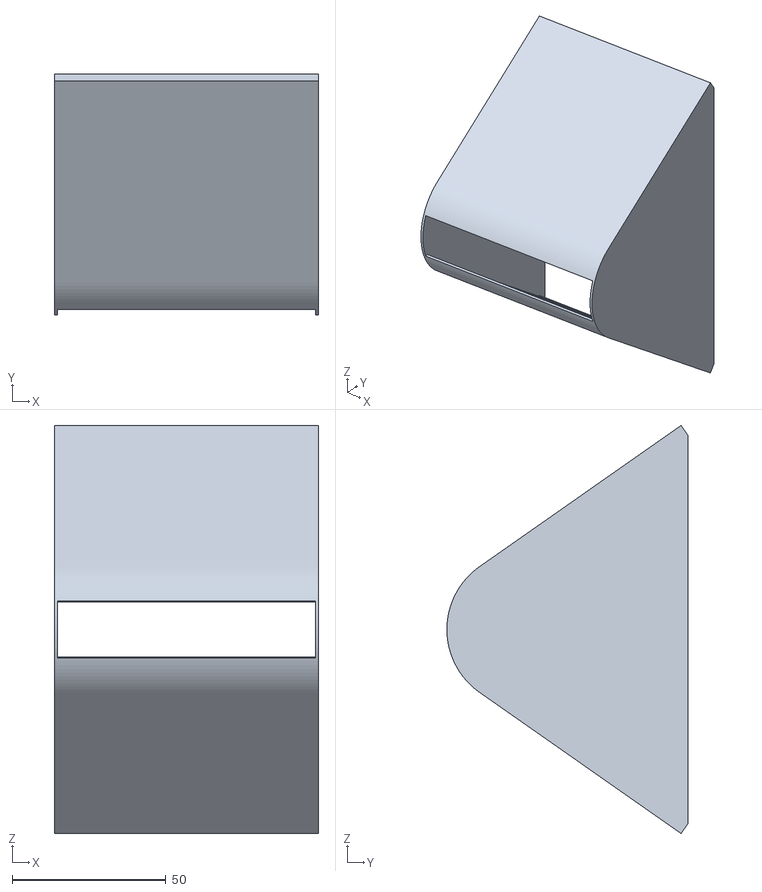
[picture p125: CAD file, 2021-07-31]
Hardware/STL/filterv3 - Part2^filterv3-1.STL
86.0 x 78.5 x 132.7
