ninicksicard/FFF_Free_Food_forever/Hardware/STL/electronic frame mount.STL

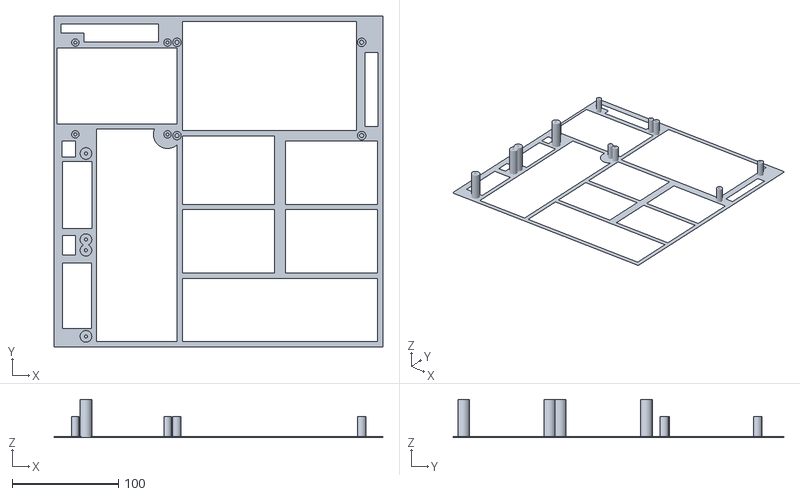
[picture p126: CAD file, 2021-07-31]
Hardware/STL/electronic frame mount.STL
309.4 x 311.4 x 36.0
