ninicksicard/FFF_Free_Food_forever/Hardware/STL/roueahaubemount.STL

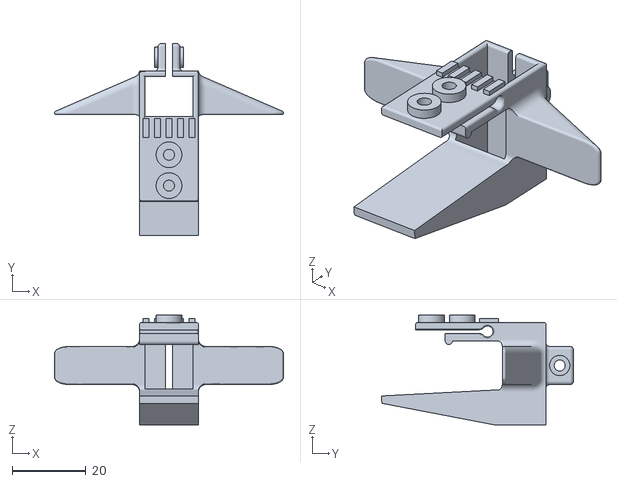
[picture p127: CAD file, 2021-07-31]
Hardware/STL/roueahaubemount.STL
62.2 x 52.2 x 29.9
