ninicksicard/FFF_Free_Food_forever/Hardware/STL/Extractor^Bioreactor - Copy of Part2^Extractor_Bioreactor-1.STL

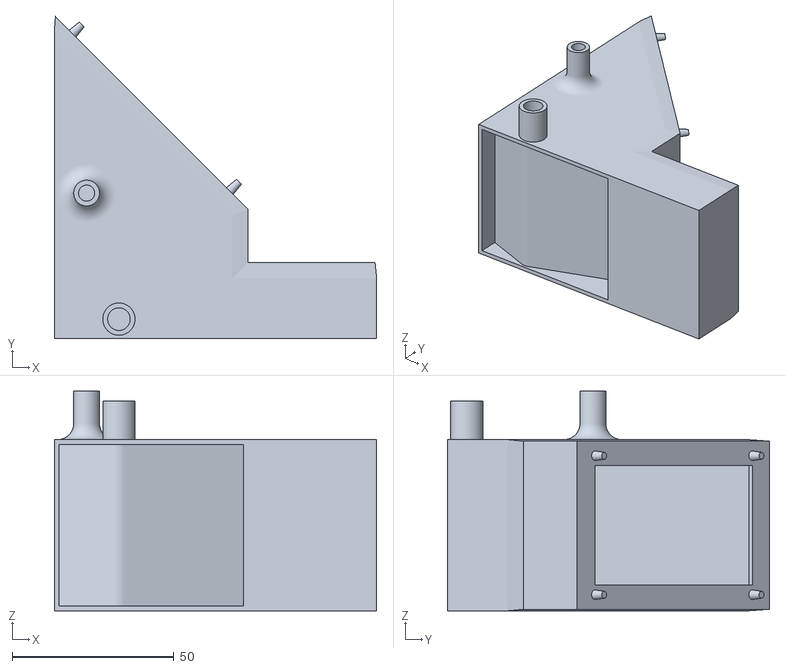
[picture p128: CAD file, 2021-07-31]
Hardware/STL/Extractor^Bioreactor - Copy of Part2^Extractor_Bioreactor-1.STL
99.8 x 99.6 x 68.0
