ninicksicard/FFF_Free_Food_forever/Hardware/STL/roue a haube.STL

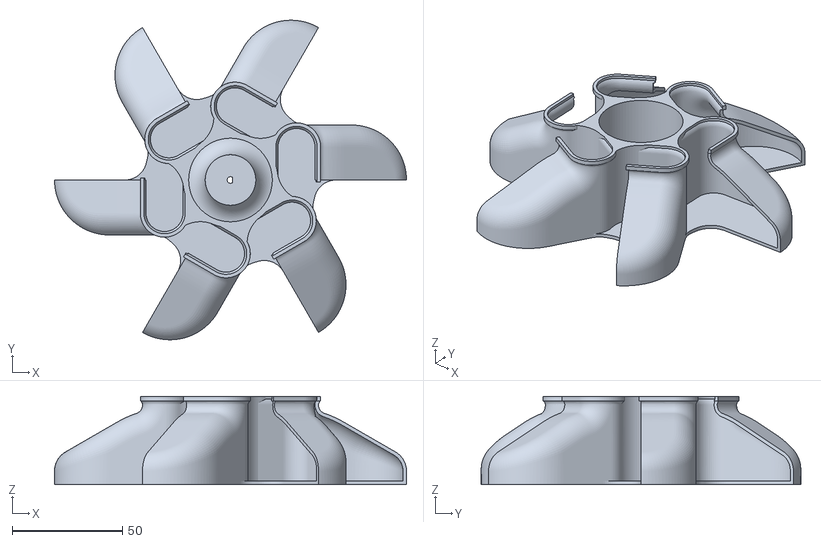
[picture p129: CAD file, 2021-07-31]
Hardware/STL/roue a haube.STL
160.0 x 145.3 x 40.0
