ninicksicard/FFF_Free_Food_forever/Hardware/STL/Extractor^Bioreactor - Part1^Extractor_Bioreactor-1.STL

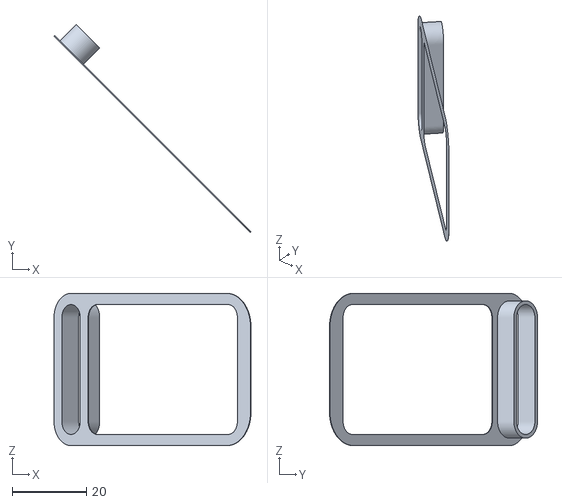
[picture p130: CAD file, 2021-07-31]
Hardware/STL/Extractor^Bioreactor - Part1^Extractor_Bioreactor-1.STL
53.1 x 56.0 x 41.0
