ninicksicard/FFF_Free_Food_forever/Hardware/STL/pump mount.STL

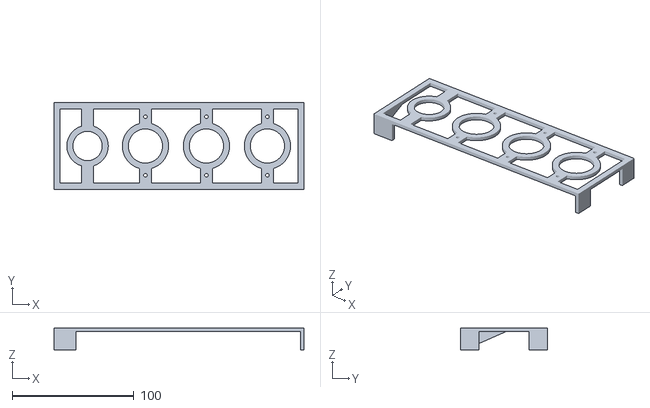
[picture p131: CAD file, 2021-07-31]
Hardware/STL/pump mount.STL
205.0 x 71.0 x 18.0
