ninicksicard/FFF_Free_Food_forever/Hardware/STL/roue a haube_adjustement rack.STL

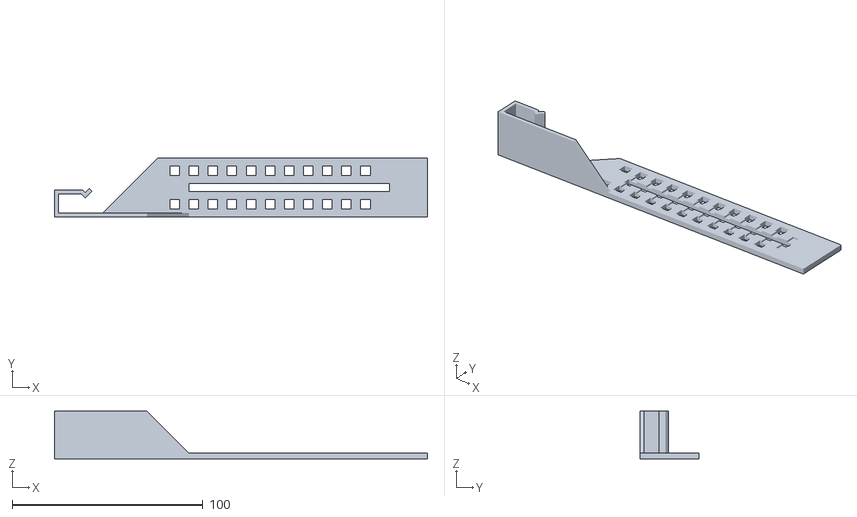
[picture p132: CAD file, 2021-05-25]
Hardware/STL/roue a haube_adjustement rack.STL
195.5 x 30.8 x 25.0
