ninicksicard/FFF_Free_Food_forever/Hardware/STL/oueahaube_crochet.STL

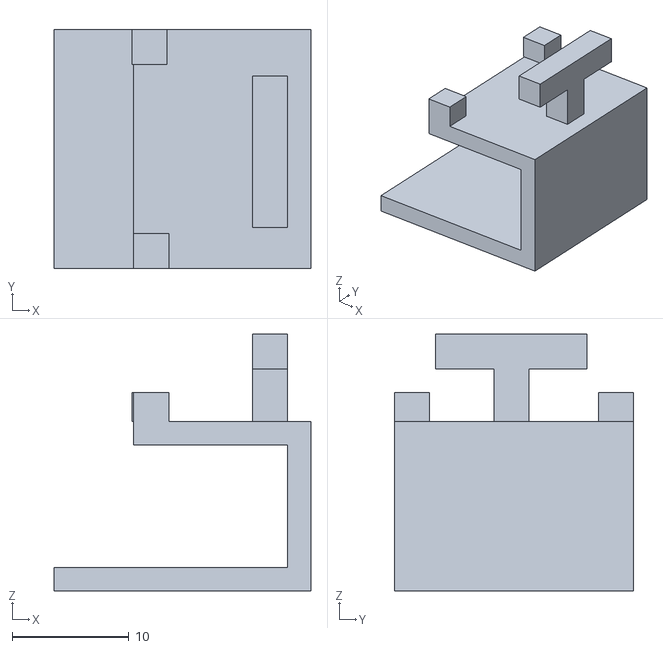
[picture p133: CAD file, 2021-05-25]
Hardware/STL/oueahaube_crochet.STL
22.0 x 20.5 x 22.0
