ninicksicard/FFF_Free_Food_forever/Software/CyanO_esp32_MicroPython/sensors.py

import machine

class Sensors:
    def __init__(self):
        # Initialize sensors
        self.sensors = {
            "culture_high_level": machine.ADC(machine.Pin(0)),  # Assuming this is an analog sensor connected to pin 0
            "nutrient_low_level": machine.ADC(machine.Pin(1))  # Assuming this is an analog sensor connected to pin 1
        }

    def setup_sensors(self, settings):
        # Setup sensors based on settings
        for sensor, setting in settings.items():
            # Here you can setup each sensor based on its settings
            pass

    def check_sensors(self):
        # Check sensors and return readings
        readings = {}
        for sensor, adc in self.sensors.items():
            readings[sensor] = adc.read()
        return readings
