ninicksicard/FFF_Free_Food_forever/Software/HA_DeviceTemplate/ESP32S3_IO_MAPPING.py

# from ESP32S3_IO_MAPPING import *
AI0=1
AI1=2
AI2=3
AI3=4
AI4=5
AI5=6
AI6=None
AI7=None
AI8=7
AI9=8
AI10=9


DI0=1
DI1=2
DI2=3
DI3=4
DI4=5
DI5=6
DI6=43
DI7=44
DI8=7
DI9=8
DI10=9

DO0=1
DO1=2
DO2=3
DO3=4
DO4=5
DO5=6
DO6=43
DO7=44
DO8=7
DO9=8
DO10=9

AO0=1
AO1=2
AO2=3
AO3=4
AO4=5
AO5=6
AO6=None
AO7=None
AO8=7
AO9=None
AO10=None
