ninicksicard/FFF_Free_Food_forever/Software/Microcontroler_Simplified/00_Loging.ino

bool Log = false;
void Serialprint(String toprint){
  if (Log){
    Serial.print(toprint);
  }
}
void Serialprintln(String toprint){
  if (Log){
    Serial.println(toprint);
  }
}


// generalized functions to read and write to the internal memory
void eeWriteInt(int pos, int val) {
    byte* p = (byte*) &val;
    EEPROM.write(pos, *p);
    EEPROM.write(pos + 1, *(p + 1));
    EEPROM.write(pos + 2, *(p + 2));
    EEPROM.write(pos + 3, *(p + 3));
    EEPROM.commit();
}

int eeGetInt(int pos) {
  int val;
  byte* p = (byte*) &val;
  *p        = EEPROM.read(pos);
  *(p + 1)  = EEPROM.read(pos + 1);
  *(p + 2)  = EEPROM.read(pos + 2);
  *(p + 3)  = EEPROM.read(pos + 3);
  return val;
}
