ninicksicard/FFF_Free_Food_forever/docs/progression medias/first inoculation.jpg

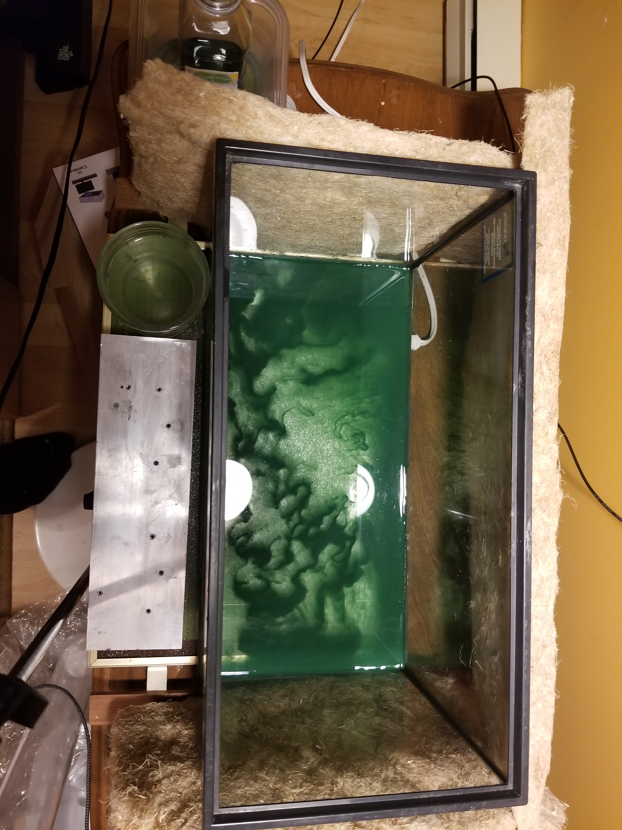
docs/progression medias/first inoculation.jpg
